teknoprep/racecar-35/hardware/_archive/README.md

# Retired A/B hardware work — not current fabrication deliverables

The active design target is **Rev C**, in `../teensy-integrated-revc/`.

- `teensy-carrier-reva/`: former, unbuilt external-module carrier. Preserved
  unchanged because the C illustration reuses its footprint/3D assets. Its
  Gerbers are NOT the integrated C design. Do not order it as a substitute.
- `teensy-integrated-revb-RETIRED-CONCEPT.tar.gz`: complete snapshot of the former
  B concept (external WiFi antenna, terminals on multiple edges). Superseded.

A/B user-facing Downloads packages were moved into
`/home/chris/Downloads/.retired-racecar-ab/` to prevent accidental ordering.
Nothing here is a Rev C electrical design, circuit approval or fabrication release.
Keep these inputs archival; old scripts may contain historical absolute paths.
