teknoprep/racecar-35/hardware/_archive/teensy-carrier-reva/reports/drill-report.txt

Drill report for racecar-carrier-reva.kicad_pcb
Created on 2026-09-09T08:36:47-0400

Copper Layer Stackup:
    =============================================================
    L1 :  F.Cu                      front
    L2 :  B.Cu                      back

Drill file 'racecar-carrier-reva-PTH.drl' contains
    plated through holes:
    =============================================================
    T1  0.400mm  0.0157"  (11 holes)
    T2  0.800mm  0.0315"  (4 holes)
    T3  0.950mm  0.0374"  (12 holes)
    T4  1.000mm  0.0394"  (78 holes)
    T5  1.300mm  0.0512"  (8 holes)

    Total plated holes count 113

Drill file 'racecar-carrier-reva-NPTH.drl' contains
    unplated through holes:
    =============================================================
    T1  3.200mm  0.1260"  (4 holes)

    Total unplated holes count 4
