teknoprep/racecar-35/crowpanel-arduino/RaceDash_v0139_orig/RaceDash_v0139_orig.ino

// racecar-35 dash — CrowPanel ESP32-S3 7" V3.0
// Built via arduino-cli with esp32:esp32@2.0.14, OPI PSRAM, QIO 4MB.
//
// UART0 (Serial) listens for two line types from the Teensy 4.1, 115200 8N1:
//   GPS,<fix>,<sats>,<lat_deg>,<lon_deg>,<speed_mph>,<heading_deg>,<gps_status>
//   ENG,<rpm>[,<oil_psi_x10>,<coolant_f_x10>]   (3-field form, back-compat to 1)
//
// Two pages, swipeable:
//   PAGE_DASH      — RPM bar + huge speed + L (HDG/LAT/LON) / R (FIX/SATS/GPS)
//   PAGE_SETTINGS  — adjustable thresholds for the RPM bar, alert thresholds,
//                    blink rates and colors. Persisted to NVS via Preferences.
// Swipe right→left enters settings; left→right returns to dash.

#include <Wire.h>
#include <PCA9557.h>
#include <WiFi.h>          // ESP32-S3 built-in WiFi (NTP, OTA HTTPS, future cloud upload)
#include <WiFiClientSecure.h>   // HTTPS to GitHub for manifest + firmware download
#include <HTTPClient.h>         // wraps WiFiClientSecure with a simple GET/POST API
#include <Update.h>             // partition-swap OTA writer
#include <esp_log.h>       // for esp_log_level_set("wifi", ESP_LOG_NONE)
#include <mbedtls/sha256.h>     // OTA artifact integrity check vs manifest sha256

// Compile-time firmware version. Bump via the release process when shipping
// a new build (eventually automated by scripts/release.sh + GitHub Action).
// Settings page displays it; "Check for updates" compares to manifest.json
// from https://raw.githubusercontent.com/teknoprep/racecar-35/main/firmware/.
#define FIRMWARE_VERSION "0.1.39"

#include <Preferences.h>
#include <time.h>
#include <driver/i2c.h>           // I2C_NUM_1 for Touch_GT911 config
#define LGFX_USE_V1
#include <LovyanGFX.hpp>
#include <lgfx/v1/platforms/esp32s3/Panel_RGB.hpp>
#include <lgfx/v1/platforms/esp32s3/Bus_RGB.hpp>

// ---------------------------------------------------------------------------
// Forward type decls — Arduino IDE auto-injects function prototypes at the
// top of the translation unit, so any type used in a function signature must
// be visible BEFORE the first function. Real definitions follow below.
// ---------------------------------------------------------------------------
enum SettingId : uint8_t {
    // Internet block at the very top — picks whether all internet-bound
    // operations route via Teensy/W5500 (Ethernet) or CrowPanel/ESP32-S3 WiFi.
    // SSID/pass/status rows are hidden when Mode=Ethernet.
    ST_INET_MODE = 0,
    ST_WIFI_SSID, ST_WIFI_PASS, ST_WIFI_STATUS,
    ST_RPM_MIN, ST_RPM_MAX, ST_ALERTS,
    ST_A1_RPM, ST_A1_COL, ST_A1_HZ,
    ST_AM_RPM, ST_AM_COL, ST_AM_HZ,
    // Coolant temp warn-color + oil PSI warn-color. Each has a master
    // show toggle, a threshold (°F or PSI), and the warning palette colour.
    ST_SHOW_TEMP, ST_TEMP_WARN_F, ST_TEMP_WARN_COL,
    ST_SHOW_PSI,  ST_PSI_WARN_PSI, ST_PSI_WARN_COL,
    // Sensor data source (Direct / MegaSquirt) + AFR display (MS3 mode only).
    // AFR has both a "too rich" (low) and "too lean" (high) warn threshold;
    // either fires the same colour.
    ST_SENSOR_TYPE,
    ST_SHOW_AFR, ST_AFR_WARN_LO, ST_AFR_WARN_HI, ST_AFR_WARN_COL,
    ST_REC_SD, ST_REC_CLOUD,
    ST_CL_HOST, ST_CL_PORT, ST_CL_PROTO, ST_CL_STREAM,
    ST_CL_AUTH_USER, ST_CL_AUTH_PASS,
    ST_AUTO_TRACK,
    ST_TIMEZONE,    // ENUM: cycle through TIMEZONES[]
    ST_SET_TIME,    // action: open time-set page
    ST_COUNT,
    // Tool-page actions — NOT in the scrollable settings list. They live on
    // PAGE_TOOLS (swipe right from STATUS). Their SettingId values are still
    // useful as keyboard / tap dispatch keys (e.g. ST_OTA_CHECK is what
    // handleSettingsTap looked for; now it's tools/handleToolsTap).
    ST_SD_FORMAT,
    ST_OTA_CHECK,
};
struct NumBounds { uint16_t lo, hi, step; };

// Forward-declared so any auto-prototype generated by the Arduino IDE for
// functions that take a `const TimeZone&` parameter resolves cleanly. The
// full struct definition lives further down with the timezone tables.
struct TimeZone;

// WiFi state machine values (full definition lives next to its tick function
// further down). Forward-declared here because the Arduino IDE / arduino-cli
// auto-injects function prototypes at the top of the TU — anything used in
// a function signature must be visible before the first function.
enum WifiState : uint8_t { WS_OFF = 0, WS_CONNECTING, WS_CONNECTED, WS_FAILED };

// Forward decls for the dash-initiated upload flow. The enum / structs need to
// be visible to the auto-prototype scanner that runs on the first function in
// the TU. wifiConnectedNow() is a helper for ufDoPost so it doesn't have to
// reach into the file-scope `wifi_state` global from above its definition.
enum UploadFlowState : uint8_t {
    UF_IDLE = 0,
    UF_LISTING,         // Q,LIST sent, awaiting Q,FILE / Q,END
    UF_FETCH_HEAD,      // Q,GET sent, awaiting Q,DATA
    UF_STREAMING,       // open TCP socket, writing bytes as Q,L arrives
    UF_STREAM_FINISH,   // EOF sent, draining HTTP response from socket
    UF_DELETING,        // Q,DEL sent, awaiting Q,DEL,OK
    UF_DONE,
};
enum SessionsListState : uint8_t {
    SL_IDLE = 0, SL_LISTING, SL_DELETING,
};
static bool wifiConnectedNow();

// Single key descriptor for both numeric and text keyboards.
struct KbKey {
    int16_t  x, y, w, h;
    const char* label;
    // action: visible char (0..0x7F) is inserted as that char into editBuf.
    // Special codes: 0x01='\b' backspace, 0x02='C' clear, 0x03='D' done,
    //                0x04='X' cancel, 0x05=' ' space.
    char action;
};

#define TFT_BL 2

PCA9557 Out;
Preferences prefs;

// ---------------------------------------------------------------------------
// LovyanGFX driver — V3.0 panel timings + GT911 capacitive touch on I2C 0x14.
// ---------------------------------------------------------------------------
class LGFX : public lgfx::LGFX_Device {
public:
    lgfx::Bus_RGB     _bus_instance;
    lgfx::Panel_RGB   _panel_instance;
    lgfx::Light_PWM   _light_instance;
    lgfx::Touch_GT911 _touch_instance;

    LGFX(void) {
        {
            auto cfg = _panel_instance.config();
            cfg.memory_width  = 800; cfg.memory_height = 480;
            cfg.panel_width   = 800; cfg.panel_height  = 480;
            cfg.offset_x = 0;        cfg.offset_y = 0;
            _panel_instance.config(cfg);
        }
        {
            auto cfg = _bus_instance.config();
            cfg.panel = &_panel_instance;
            cfg.pin_d0  = GPIO_NUM_15; cfg.pin_d1  = GPIO_NUM_7;  cfg.pin_d2  = GPIO_NUM_6;
            cfg.pin_d3  = GPIO_NUM_5;  cfg.pin_d4  = GPIO_NUM_4;
            cfg.pin_d5  = GPIO_NUM_9;  cfg.pin_d6  = GPIO_NUM_46; cfg.pin_d7  = GPIO_NUM_3;
            cfg.pin_d8  = GPIO_NUM_8;  cfg.pin_d9  = GPIO_NUM_16; cfg.pin_d10 = GPIO_NUM_1;
            cfg.pin_d11 = GPIO_NUM_14; cfg.pin_d12 = GPIO_NUM_21; cfg.pin_d13 = GPIO_NUM_47;
            cfg.pin_d14 = GPIO_NUM_48; cfg.pin_d15 = GPIO_NUM_45;
            cfg.pin_henable = GPIO_NUM_41;
            cfg.pin_vsync   = GPIO_NUM_40;
            cfg.pin_hsync   = GPIO_NUM_39;
            cfg.pin_pclk    = GPIO_NUM_0;
            cfg.freq_write  = 15000000;
            cfg.hsync_polarity    = 0;
            cfg.hsync_front_porch = 40;
            cfg.hsync_pulse_width = 48;
            cfg.hsync_back_porch  = 40;
            cfg.vsync_polarity    = 0;
            cfg.vsync_front_porch = 1;
            cfg.vsync_pulse_width = 31;
            cfg.vsync_back_porch  = 13;
            cfg.pclk_active_neg = 1;
            cfg.de_idle_high    = 0;
            cfg.pclk_idle_high  = 0;
            _bus_instance.config(cfg);
            _panel_instance.setBus(&_bus_instance);
        }
        {
            auto cfg = _light_instance.config();
            cfg.pin_bl = GPIO_NUM_2;
            _light_instance.config(cfg);
            _panel_instance.light(&_light_instance);
        }
        {
            auto cfg = _touch_instance.config();
            cfg.x_min      = 0;   cfg.x_max = 799;
            cfg.y_min      = 0;   cfg.y_max = 479;
            cfg.pin_int    = -1;
            cfg.pin_rst    = -1;
            cfg.bus_shared = true;
            cfg.offset_rotation = 0;
            cfg.i2c_port   = I2C_NUM_1;
            cfg.pin_sda    = GPIO_NUM_19;
            cfg.pin_scl    = GPIO_NUM_20;
            cfg.freq       = 400000;
            cfg.i2c_addr   = 0x14;
            _touch_instance.config(cfg);
            _panel_instance.setTouch(&_touch_instance);
        }
        setPanel(&_panel_instance);
    }
};

LGFX tft;

// ---------------------------------------------------------------------------
// Sprite back-buffers for the dynamic dash page regions.
//
// Why: the CrowPanel V3.0 RGB Panel keeps a continuous parallel-RGB scan over
// its framebuffer in PSRAM. When we draw text/shapes directly into that
// framebuffer, the LCD can scan a half-written element and the user sees a
// tear. At 25 Hz telemetry that tear is visible 25 times per second on the
// big-area elements (speed digit, RPM bar, sensor lines).
//
// Fix: render each fast-changing region into its own PSRAM-backed sprite,
// then pushSprite() the whole sprite to the framebuffer in one DMA blit.
// The blit is fast (sub-ms for these sizes on the S3) so the LCD scan rarely
// catches a sprite mid-push, and the user-visible result is a clean atomic
// update of each element. Each sprite is allocated once at boot and reused
// for the life of the process.
//
// Sized generously so even Font7-size-4 "888" (full speed digit) or a long
// "TEMP: 250\xB0F" line fits without clipping.
// ---------------------------------------------------------------------------
namespace {
    LGFX_Sprite spr_rpm_bar(&tft);     // inside the RPM bar border
    LGFX_Sprite spr_rpm_text(&tft);    // RPM number under the bar
    LGFX_Sprite spr_speed(&tft);       // huge centred MPH digits
    LGFX_Sprite spr_temp(&tft);        // "TEMP: ..." line
    LGFX_Sprite spr_psi(&tft);         // "PSI:  ..." line
    LGFX_Sprite spr_afr(&tft);         // "AFR:  ..." line (MS3 mode only)
    LGFX_Sprite spr_rec_badge(&tft);   // REC ● N  /  queue: N  /  REC ? no ack
    LGFX_Sprite spr_fix(&tft);         // FIX value (right column)
    LGFX_Sprite spr_sats(&tft);        // SATS value (right column)
    LGFX_Sprite spr_gps(&tft);         // GPS status value (right column)
    LGFX_Sprite spr_pred(&tft);        // predictive lap time (middle column)
    LGFX_Sprite spr_lap(&tft);         // last lap time (middle column)
    LGFX_Sprite spr_track_name(&tft);  // active track name under TRACK btn
    LGFX_Sprite spr_recbtn(&tft);      // START/STOP button face
    LGFX_Sprite spr_upbtn(&tft);       // manual queue-upload button
}
static bool   dash_sprites_ready = false;

static void setupDashSprites() {
    auto mk = [](LGFX_Sprite& s, int w, int h) -> bool {
        s.setPsram(true);          // request PSRAM backing store
        s.setColorDepth(16);       // match RGB565 panel format
        return s.createSprite(w, h) != nullptr;
    };
    // Inner-of-border for the RPM bar so the static white border outline
    // drawn directly on the framebuffer at pageJustEntered isn't clobbered.
    dash_sprites_ready =
        mk(spr_rpm_bar,    756, 76)  &&
        mk(spr_rpm_text,   110, 26)  &&
        mk(spr_speed,      360, 200) &&    // covers Font7-size-4 (≈192 px tall)
        mk(spr_temp,       240, 38)  &&
        mk(spr_psi,        240, 38)  &&
        mk(spr_afr,        240, 38)  &&
        mk(spr_rec_badge,  220, 22)  &&
        mk(spr_fix,        110, 24)  &&
        mk(spr_sats,        60, 24)  &&
        mk(spr_gps,        110, 24)  &&
        mk(spr_pred,       110, 24)  &&
        mk(spr_lap,        110, 24)  &&
        mk(spr_track_name, 320, 22)  &&
        mk(spr_recbtn,     160, 70)  &&
        mk(spr_upbtn,      180, 70);
    if (dash_sprites_ready) Serial.println("dash sprites: ok");
    else                    Serial.println("WARNING: dash sprite alloc failed \u2014 dash will fall back to direct draw");
}

// ---------------------------------------------------------------------------
// User-pickable color palette for alert colors.
// ---------------------------------------------------------------------------
constexpr int N_PALETTE = 8;
const uint16_t PALETTE[N_PALETTE] = {
    TFT_RED, TFT_ORANGE, TFT_YELLOW, TFT_GREEN,
    TFT_CYAN, TFT_BLUE, TFT_MAGENTA, TFT_WHITE
};
const char* const PALETTE_NAMES[N_PALETTE] = {
    "RED", "ORANGE", "YELLOW", "GREEN",
    "CYAN", "BLUE", "MAGENTA", "WHITE"
};

// ---------------------------------------------------------------------------
// State.
// ---------------------------------------------------------------------------
struct GpsState {
    uint8_t  fix      = 0;
    uint8_t  sats     = 0;
    float    lat_deg  = 0.0f;
    float    lon_deg  = 0.0f;
    float    mph      = 0.0f;
    float    hdg_deg  = 0.0f;
    uint8_t  status   = 0;        // 0=OFF 1=RAW 2=OK 3=STALE
    uint32_t last_ms  = 0;
};
static GpsState g;

struct EngState {
    uint16_t rpm           = 0;
    // x10 fixed-point: 0..30000 PSI*10, -1 on sensor fault. Stored as int16.
    int16_t  oil_psi_x10   = -1;
    int16_t  coolant_f_x10 = -1;
    uint32_t last_ms       = 0;
};
static EngState eng;

// MegaSquirt-via-CAN data, forwarded by the Teensy when the CAN transceiver is
// wired up (planned — see Teensy main.cpp). All fields are x10 fixed-point
// except RPM. -1 indicates "not received" / fault. The dash listens for ECU
// lines only when settings.sensor_type == 1 (MegaSquirt).
struct EcuState {
    uint16_t rpm           = 0;
    int16_t  coolant_f_x10 = -1;
    int16_t  map_x10       = -1;     // manifold absolute pressure, kPa × 10
    int16_t  tps_x10       = -1;     // throttle position, % × 10
    int16_t  afr_x10       = -1;     // air/fuel ratio × 10 (e.g. 145 = 14.5)
    int16_t  iat_f_x10     = -1;     // intake air temp, °F × 10
    int16_t  bat_x10       = -1;     // battery voltage, V × 10
    uint32_t last_ms       = 0;
};
static EcuState ecu;

struct ImuState {
    float    ax = 0, ay = 0, az = 0;   // g  (±2g range)
    float    gx = 0, gy = 0, gz = 0;   // deg/s (±250 range)
    uint32_t last_ms = 0;
};
static ImuState imu;

static char     active_ip[24]    = "NOT CONNECTED";  // updated by ETH, line from Teensy
static uint32_t rec_start_ms     = 0;                // millis() when recording last started

// SD card state — updated from SD,<status>[,<total_mb>[,<free_mb>]] lines.
// 0=NONE  1=NEEDS_FORMAT  2=READY  3=ERROR  4=FORMATTING
static uint8_t  sd_card_status   = 0;
static uint32_t sd_total_mb      = 0;
static uint32_t sd_free_mb       = 0;
static char     sd_err_hex[8]    = "";   // last SdFat err code (hex from SD,NONE,<errcode>)

// Active session state — updated from SD,REC,<0|1>,<file>,<samples> lines.
// The dash uses this to show a REC indicator + a live sample count.
static bool     sd_session_active  = false;
static char     sd_session_file[80] = "";
static uint32_t sd_session_samples = 0;

// ---------------------------------------------------------------------------
// OTA state — driven by tapping "Check for updates" in settings.
// Source of truth lives in firmware/manifest.json on this repo's main branch:
//   https://raw.githubusercontent.com/teknoprep/racecar-35/main/firmware/manifest.json
//
// State machine drives PAGE_OTA modal. otaTick() in loop() advances states
// that perform network work (checking + downloading) without blocking the
// touch handler. Cancel is implemented by setting ota_cancel_requested;
// the tick checks it between chunks and bails.
// ---------------------------------------------------------------------------
enum OtaState : uint8_t {
    OTA_S_IDLE = 0,
    OTA_S_CHECKING,             // GET manifest.json
    OTA_S_UPTODATE,             // version match — nothing to do
    OTA_S_AVAILABLE,            // update found; modal waits for user Confirm/Cancel
    OTA_S_TEENSY_DOWNLOADING,   // download teensy.hex + stream over UART to Teensy
    OTA_S_TEENSY_WAITING,       // hex flushed; wait/poll until Teensy reports target version
    OTA_S_DOWNLOADING,          // streaming CrowPanel firmware bytes into Update.write()
    OTA_S_APPLYING,             // Update.end() in progress (finalising flash partition)
    OTA_S_REBOOT,               // success; about to ESP.restart()
    OTA_S_FAILED,               // any error; modal shows reason + Close
};
static OtaState ota_state              = OTA_S_IDLE;
static char     ota_latest_version[16] = "";
static char     ota_url[200]           = "";
static char     ota_err_msg[80]        = "";
static uint32_t ota_total_bytes        = 0;
static uint32_t ota_done_bytes         = 0;
static char     ota_sha256[80]         = "";   // expected sha256 from manifest (crowpanel)
static char     ota_teensy_sha256[80]  = "";   // expected sha256 from manifest (teensy)
// Teensy OTA uses two visible phases: WiFi download into PSRAM, then
// ACK-paced UART transfer to the Teensy/FlasherX. Keep separate counters so
// the modal doesn't misleadingly show one bar that suddenly slows at 50%.
static uint32_t ota_t_dl_total         = 0;
static uint32_t ota_t_dl_done          = 0;
static uint32_t ota_t_tx_total         = 0;
static uint32_t ota_t_tx_done          = 0;
static uint8_t  ota_return_page        = 0;     // page to restore on Close
static bool     ota_modal_dirty        = false;
static bool     ota_cancel_requested   = false;
// Teensy-side update state (parallel manifest entry)
static char     ota_teensy_version[16] = "";
static char     ota_teensy_url[200]    = "";
static uint32_t ota_teensy_size        = 0;
static bool     ota_need_teensy        = false;
static bool     ota_need_crowpanel     = false;
static bool     ota_teensy_commit_seen = false;   // saw FW,COMMITTING from FlasherX

// Upload modal state — driven by UPLOAD,START/PROG/DONE lines from Teensy.
// While upload_active, the dash forces PAGE_UPLOAD on top of whatever was
// showing, and ignores all input except the CANCEL button. CANCEL latches
// upload_locally_cancelled = true so the dash can show a small reminder that
// uploads are disabled until the system reboots.
static bool     upload_active            = false;
static char     upload_file[64]          = "";
static uint32_t upload_total             = 0;
static uint32_t upload_done              = 0;
static uint8_t  upload_return_page       = 0;        // PAGE_DASH; uint8_t because
                                                     // enum Page isn't visible up here
static bool     upload_locally_cancelled = false;   // cleared only on reboot
static bool     upload_modal_dirty       = false;
static uint32_t upload_last_draw_ms      = 0;
static char     upload_result_msg[180]   = "";       // banner after DONE: status + optional reason

// Cloud state — updated from CLD,<live_ok>,<queue_depth> lines.
static bool     cloud_live_ok      = false;
static uint32_t cloud_queue_depth  = 0;

// Firmware version tracking. Dash version is compile-time (FIRMWARE_VERSION).
// Teensy version arrives via VER,teensy,<ver> on Teensy boot, and on demand
// when the dash sends "VER?\n" (dash boot + status page entry).
static char     teensy_fw_version[16] = "?";

// Two-tap arming for the SD format action in settings.
static bool     sd_format_armed  = false;
static uint32_t sd_format_arm_ms = 0;

// Settings page dirty flag — declared here (before the UART parsers) so
// parseSdLine() can set it on status change. The settings page checks it
// each draw cycle to decide whether to repaint.
static bool settingsDirty = true;

// RTC epoch received from the Teensy's TIME, line (0 = not yet received).
static uint32_t rtc_epoch = 0;

// Time-set page editing state — populated from rtc_epoch on entry.
static int  ts_year  = 2025, ts_month = 1, ts_day  = 1;
static int  ts_hour  = 0,    ts_min   = 0, ts_sec  = 0;
static bool ts_dirty = false;   // set by +/- taps; triggers value redraw

// ---------------------------------------------------------------------------
// Lap timer — GPS-proximity start/finish detection + distance integration.
// ---------------------------------------------------------------------------
struct LapTimer {
    bool     active          = false;
    int      track_idx       = -1;    // which TRACKS[] entry we're timing at
    uint32_t lap_start_ms    = 0;
    float    dist_miles      = 0.0f;  // odometer this lap (mph * dt)
    uint32_t prev_gps_ms     = 0;
    bool     left_start      = false; // true once car has moved away from S/F line
    bool     timing_started  = false; // true after first clean S/F crossing (guards partial first lap)

    uint32_t last_lap_ms     = 0;     // most recent completed lap time (0 = none)
    float    last_lap_dist   = 0.0f;  // distance of last completed lap (miles)
};
static LapTimer lapTimer;

constexpr float    LAP_RADIUS_KM = 0.075f;   // 75 m start/finish detection radius
constexpr uint32_t MIN_LAP_MS    = 15000;    // minimum lap time before a crossing counts

// Recording state — toggled by the START/STOP button on the dash. Sent to
// the Teensy as `REC,<0|1>\n` on UART0 TX. The Teensy doesn't read this
// yet (one-way bytes harmlessly accumulate in its Serial3 RX buffer);
// when the SD-card / cloud-streaming feature is implemented Teensy-side
// it just starts consuming the line.
static bool recording         = false;
static int  last_track_idx    = -1;        // TRACKS[] index of the last confirmed track (-1 = none saved)
static char active_track_name[52] = "";    // full display name (may include config, e.g. "Mid-Ohio Full Course")

// Button geometry on the dash page — both buttons sit left of the speed.
// START/STOP is smaller and higher than before; TRACK button lives below it.
namespace {
  constexpr int RECBTN_X = 30;
  constexpr int RECBTN_Y = 155;
  constexpr int RECBTN_W = 160;
  constexpr int RECBTN_H = 70;
  constexpr int TRKBTN_X = 30;    // always-visible shortcut to the track picker
  constexpr int TRKBTN_Y = 235;   // RECBTN_Y + RECBTN_H + 10
  constexpr int TRKBTN_W = 160;
  constexpr int TRKBTN_H = 60;
  // Manual queue-upload button. Shows only when there is a backlog of
  // sessions waiting in /queue/ AND we aren't currently recording. Sits in
  // the empty band between the START button and the big speed digit.
  constexpr int UPBTN_X = 210;
  constexpr int UPBTN_Y = 155;
  constexpr int UPBTN_W = 180;
  constexpr int UPBTN_H = 70;
  // Speed sits on the right side of the screen (out of the way of the
  // START/STOP button on the left). Drop the decimal at >=100 mph so a
  // 3-digit number stays narrow enough to fit the 400-px bg pad cleanly
  // without clipping at the right edge.
  // Speed is integer MPH only (no decimal), so the layout never has to budget
  // for a decimal point that vanishes at >= 100 mph. With 3 digits max we can
  // pull the centre slightly inward from the right panel edge for breathing
  // room around the largest values.
  constexpr int SPEED_CX    = 580;       // speed text middle-centre x
  constexpr int SPEED_PAD_W = 360;       // bg-fill pad width (spans 400..760)
}

struct Settings {
    // RPM bar + alert flash (existing)
    uint16_t rpm_min          = 1000;
    uint16_t rpm_max          = 8000;
    bool     alerts_enabled   = true;
    uint16_t alert1_rpm       = 6000;
    uint8_t  alert1_color_idx = 2;     // YELLOW
    uint8_t  alert1_hz        = 2;
    uint16_t alertmax_rpm     = 7500;
    uint8_t  alertmax_color_idx = 0;   // RED
    uint8_t  alertmax_hz      = 8;

    // Recording / streaming
    bool     record_sd        = false;
    bool     record_cloud     = false;
    char     cloud_host[64]   = "racecar.api.blueuc.com";  // default endpoint
    uint16_t cloud_port       = 80;
    uint8_t  cloud_protocol   = 1;     // 0=HTTP, 1=HTTPS, 2=FTP (default HTTPS; FTP NYI)
    uint8_t  cloud_stream     = 1;     // 0=Live, 1=AfterRace (default AfterRace; WiFi forces AfterRace anyway)
    // cloud_user repurposed as a free-text USER EMAIL tag for data ownership.
    // Not an auth credential — the Teensy forwards it as X-User-Email header.
    // Real auth (Google OAuth) lives in the cloud-side Docker image.
    char     cloud_auth_user[64] = "";   // user email (X-User-Email)
    char     cloud_auth_pass[96] = "";   // API key (X-API-Key); masked on display

    // Internet routing. 0=Ethernet (Teensy/W5500), 1=WiFi (CrowPanel ESP32-S3).
    // Phase 1: controls NTP path + (future) firmware update path. Cloud upload
    // routing still flows through Teensy/Ethernet regardless until Phase 3.
    uint8_t  internet_mode    = 0;       // default Ethernet
    char     wifi_ssid[33]    = "";      // 802.11 max 32 + NUL
    char     wifi_pass[64]    = "";      // WPA2 PSK max 63 + NUL

    // Engine sensor display + warn thresholds (drawn bottom-left on the dash).
    // show_*  : false hides that line entirely from the dash.
    // *_warn  : threshold past which the value flips to the warn colour.
    //           Coolant warns ABOVE the threshold (overheat), oil warns BELOW
    //           it (low pressure — engine-killing if you don't see it).
    bool     show_coolant       = true;
    uint16_t coolant_warn_f     = 220;     // °F — typical 220°F overheat threshold
    uint8_t  coolant_warn_col   = 0;       // RED
    bool     show_oil_psi       = true;
    uint16_t oil_warn_psi       = 20;      // PSI — typical 20 PSI low-oil floor
    uint8_t  oil_warn_col       = 0;       // RED

    // Sensor data source. Selects which UART line type the dash trusts for
    // engine telemetry that exists in both pipelines (coolant temp today; RPM
    // and others as MS3 CAN comes online):
    //   0 = Direct     — Teensy ADCs on A2/A3 (the wiring we built in §5b/5c)
    //   1 = MegaSquirt — MS3 CAN broadcast, forwarded by Teensy as ECU,...
    // Oil PSI stays direct regardless (MS3 typically doesn't have an oil
    // pressure input wired). AFR is only available in MegaSquirt mode.
    uint8_t  sensor_type        = 0;       // default Direct

    // AFR (Air/Fuel Ratio) — only meaningful in MegaSquirt sensor mode.
    // Two-sided warn band: too rich (< afr_warn_lo) and too lean (> afr_warn_hi)
    // both flip the value to the warn colour. Values are AFR × 10 (so 145 = 14.5).
    bool     show_afr           = true;
    uint16_t afr_warn_lo_x10    = 115;     // 11.5 AFR — below this is dangerously rich
    uint16_t afr_warn_hi_x10    = 160;     // 16.0 AFR — above this is dangerously lean
    uint8_t  afr_warn_col       = 0;       // RED

    // Track selection
    bool     auto_select_track = true; // when on, skip picker if a clear closest match exists

    // Time zone — index into TIMEZONES[] (defined below). Display only;
    // the Teensy's RTC + the wire-format TIME line are always UTC.
    uint8_t  timezone_idx     = 0;     // default UTC
};
static Settings s;

// Names for ENUM-style settings (cycle-on-tap).
const char* const PROTOCOL_NAMES[] = { "HTTP", "HTTPS", "FTP" };
constexpr int N_PROTOCOL = 3;
const char* const STREAM_NAMES[]   = { "Live Stream", "After Race" };
constexpr int N_STREAM   = 2;
const char* const SENSOR_TYPE_NAMES[] = { "Direct", "MegaSquirt" };
constexpr int N_SENSOR_TYPE = 2;
const char* const INET_MODE_NAMES[]   = { "Ethernet", "WiFi" };
constexpr int N_INET_MODE   = 2;

// ---------------------------------------------------------------------------
// Time zones with DST rules.
//
// The Teensy emits UTC always (TIME,<unix_epoch>). All DST/offset math is
// done here in the dash for display purposes. We send TZ,<id> to the Teensy
// at boot and on change so the trunk-side has the info available for future
// SD-filename / cloud-metadata use, but the Teensy doesn't currently apply
// the offset itself.
//
// DST rule fields:
//   stdOffsetHr   standard-time offset from UTC in hours (-5 = EST, +0 = GMT)
//   observesDst   true if DST applies (false for AZ, HI, UTC, etc.)
//   dstStart{Month,Week,Dow,Hour}   "Nth weekday of month, at HH local std time"
//   dstEnd{Month,Week,Dow,Hour}     same shape; week 1-4 = nth, 5 = last
// ---------------------------------------------------------------------------
struct TimeZone {
    const char* id;            // short id sent to Teensy ("UTC", "ET", "PT", ...)
    const char* name;          // long name shown in the settings ENUM cycle
    const char* abbrevStd;     // abbreviation when in standard time ("EST")
    const char* abbrevDst;     // abbreviation when in DST ("EDT"); == abbrevStd if no DST
    int8_t      stdOffsetHr;
    bool        observesDst;
    uint8_t     dstStartMonth;  // 1-12
    uint8_t     dstStartWeek;   // 1-4 (nth) or 5 (last)
    uint8_t     dstStartDow;    // 0=Sun .. 6=Sat
    uint8_t     dstStartHour;   // local std hour at which DST begins
    uint8_t     dstEndMonth;
    uint8_t     dstEndWeek;
    uint8_t     dstEndDow;
    uint8_t     dstEndHour;
};

// Common US zones + a few internationals. Add more by extending this array.
// US DST: 2nd Sunday of March → 1st Sunday of November (since 2007).
// EU DST: last Sunday of March → last Sunday of October.
static const TimeZone TIMEZONES[] = {
    // id      name                  std    dst    off  dst   sM sW sD sH eM eW eD eH
    { "UTC",   "UTC",                "UTC", "UTC",  0,  false, 0, 0, 0, 0, 0, 0, 0, 0 },
    { "ET",    "Eastern (US)",       "EST", "EDT", -5, true,   3, 2, 0, 2, 11, 1, 0, 2 },
    { "CT",    "Central (US)",       "CST", "CDT", -6, true,   3, 2, 0, 2, 11, 1, 0, 2 },
    { "MT",    "Mountain (US)",      "MST", "MDT", -7, true,   3, 2, 0, 2, 11, 1, 0, 2 },
    { "MT-AZ", "Arizona (no DST)",   "MST", "MST", -7, false,  0, 0, 0, 0, 0, 0, 0, 0 },
    { "PT",    "Pacific (US)",       "PST", "PDT", -8, true,   3, 2, 0, 2, 11, 1, 0, 2 },
    { "AKT",   "Alaska",             "AKST","AKDT",-9, true,   3, 2, 0, 2, 11, 1, 0, 2 },
    { "HT",    "Hawaii (no DST)",    "HST", "HST",-10, false,  0, 0, 0, 0, 0, 0, 0, 0 },
    { "GMT",   "UK (London)",        "GMT", "BST",  0, true,   3, 5, 0, 1, 10, 5, 0, 1 },
    { "CET",   "Europe (Paris)",     "CET", "CEST", 1, true,   3, 5, 0, 2, 10, 5, 0, 2 },
};
constexpr int N_TIMEZONES = sizeof(TIMEZONES) / sizeof(TIMEZONES[0]);

// Days in month (Gregorian). Leap years = divisible by 4 except centuries
// not divisible by 400.
static int daysInMonth(int y, int m) {
    static const int dom[] = {0,31,28,31,30,31,30,31,31,30,31,30,31};
    const bool leap = (y % 4 == 0 && y % 100 != 0) || (y % 400 == 0);
    return (m == 2 && leap) ? 29 : dom[m];
}

// Day-of-week for a Gregorian date. Zeller's congruence, normalised to
// 0=Sunday, 1=Monday ... 6=Saturday.
static int dayOfWeek(int y, int m, int d) {
    if (m < 3) { y--; m += 12; }
    const int K = y % 100;
    const int J = y / 100;
    const int h = (d + (13 * (m + 1)) / 5 + K + K / 4 + J / 4 + 5 * J) % 7;
    // Zeller h: 0=Sat, 1=Sun, 2=Mon, ..., 6=Fri → shift to 0=Sun
    return (h + 6) % 7;
}

// Day-of-month for the Nth occurrence of a given weekday in a given month.
// nth: 1..4 = literal, 5 = "last".
static int nthWeekdayOfMonth(int year, int month, int targetDow, int nth) {
    const int firstDow         = dayOfWeek(year, month, 1);
    const int firstOccurrence  = ((targetDow - firstDow + 7) % 7) + 1;
    if (nth >= 5) {
        // Last occurrence: walk forward by 7 until next would overshoot the month.
        const int dim = daysInMonth(year, month);
        int d = firstOccurrence;
        while (d + 7 <= dim) d += 7;
        return d;
    }
    return firstOccurrence + 7 * (nth - 1);
}

// Is DST currently in effect for the given UTC epoch under the given zone?
// We compare against local *standard* time so the rule's "2 AM local" maps
// cleanly to a single instant per year (we don't try to resolve the
// 2:00–3:00 AM "spring-forward" gap or 1:00–2:00 AM "fall-back" overlap;
// those edge cases are sub-second and not worth the complexity here).
static bool isDstActive(time_t utc, const TimeZone& tz) {
    if (!tz.observesDst) return false;

    const time_t   localStd = utc + (time_t)tz.stdOffsetHr * 3600;
    struct tm*     tmv = gmtime(&localStd);
    const int year  = tmv->tm_year + 1900;
    const int month = tmv->tm_mon + 1;
    const int day   = tmv->tm_mday;
    const int hour  = tmv->tm_hour;

    const int dstStartDay = nthWeekdayOfMonth(year, tz.dstStartMonth, tz.dstStartDow, tz.dstStartWeek);
    const int dstEndDay   = nthWeekdayOfMonth(year, tz.dstEndMonth,   tz.dstEndDow,   tz.dstEndWeek);

    // Outside the months containing the transitions: easy.
    if (month > tz.dstStartMonth && month < tz.dstEndMonth) return true;
    if (month < tz.dstStartMonth || month > tz.dstEndMonth) return false;

    // Same month as start (or end): compare day, then hour.
    if (month == tz.dstStartMonth) {
        if (day != dstStartDay) return day > dstStartDay;
        return hour >= tz.dstStartHour;
    }
    // month == dstEndMonth
    if (day != dstEndDay) return day < dstEndDay;
    return hour < tz.dstEndHour;
}

// UTC offset in seconds (negative for west of UTC), accounting for DST.
static int32_t tzOffsetSeconds(time_t utc, const TimeZone& tz) {
    int32_t off = (int32_t)tz.stdOffsetHr * 3600;
    if (isDstActive(utc, tz)) off += 3600;
    return off;
}

// UTC → local epoch (seconds). Result can be passed to gmtime() to format.
static time_t utcToLocal(time_t utc, const TimeZone& tz) {
    return utc + tzOffsetSeconds(utc, tz);
}

// Local → UTC. Used when the user hand-enters a time via the time-set page.
// Computes the offset by approximating DST status from a near-UTC estimate;
// only ambiguous within the spring/fall transition hour, which we accept.
static time_t localToUtc(time_t local, const TimeZone& tz) {
    int32_t off = (int32_t)tz.stdOffsetHr * 3600;
    const time_t utcApprox = local - off;
    if (isDstActive(utcApprox, tz)) off += 3600;
    return local - off;
}

// Returns the abbreviation appropriate for the given UTC moment ("EST"/"EDT").
static const char* tzAbbrevFor(time_t utc, const TimeZone& tz) {
    return isDstActive(utc, tz) ? tz.abbrevDst : tz.abbrevStd;
}

// Build a UTC unix epoch from broken-down UTC fields. (Used by time-set SAVE.)
static uint32_t makeEpochUtc(int y, int mo, int d, int h, int mi, int s) {
    static const int dom[] = {0,31,28,31,30,31,30,31,31,30,31,30,31};
    uint32_t days = 0;
    for (int yr = 1970; yr < y; yr++) {
        days += 365 + (((yr % 4 == 0 && yr % 100 != 0) || yr % 400 == 0) ? 1 : 0);
    }
    for (int m = 1; m < mo; m++) {
        days += dom[m];
        if (m == 2 && ((y % 4 == 0 && y % 100 != 0) || y % 400 == 0)) days++;
    }
    days += d - 1;
    return (uint32_t)days * 86400UL + (uint32_t)h * 3600UL + (uint32_t)mi * 60UL + (uint32_t)s;
}

// ---------------------------------------------------------------------------
// Track database — pre-seeded list of common US road-course tracks. Stored
// alphabetically (the picker re-orders on the fly when GPS is available).
// Add tracks by extending this array OR (TODO) editing via the settings page.
// ---------------------------------------------------------------------------
struct TrackConfig { const char* name; };

struct TrackInfo {
    const char* name;
    float       lat;                    // track centre (used for "are you at this track?")
    float       lon;
    float       radius_km;
    float       sf_lat;                 // start/finish line (used for lap detection)
    float       sf_lon;                 // NOTE: all S/F coords are approximate — verify on-site
    const TrackConfig* configs;         // nullptr = single layout, no config sub-picker
    uint8_t            n_configs;       // 0 = single layout
};
// Config arrays — tracks with multiple layouts that share the same S/F line.
// Layouts with genuinely different S/F locations get separate TRACKS[] entries.
static const TrackConfig MID_OHIO_CFGS[] = { {"Full + Chicane"}, {"Full Course"}, {"Short Course"} };
static const TrackConfig SONOMA_CFGS[]   = { {"Full Course"}, {"Short Course"} };
static const TrackConfig WGL_CFGS[]      = { {"Grand Prix"}, {"Short Course"} };
static const TrackConfig VIR_CFGS[]      = { {"Full Course"}, {"Grand Course"}, {"North Course"} };

static const TrackInfo TRACKS[] = {
    // name                     centre lat/lon           radius  S/F lat/lon               configs       n
    { "Barber",        33.5328f,  -86.6181f, 2.5f,  33.5327f,  -86.6155f, nullptr,         0 },
    { "CMP Full",      34.4884f,  -80.5941f, 2.0f,  34.4870f,  -80.5955f, nullptr,         0 },
    { "CMP East",      34.4870f,  -80.5880f, 1.2f,  34.4840f,  -80.5880f, nullptr,         0 },
    { "CMP West",      34.4884f,  -80.6000f, 1.0f,  34.4900f,  -80.6000f, nullptr,         0 },
    { "COTA",          30.1328f,  -97.6411f, 3.0f,  30.1341f,  -97.6413f, nullptr,         0 },
    { "Daytona",       29.1853f,  -81.0697f, 3.0f,  29.1868f,  -81.0700f, nullptr,         0 },
    { "Laguna Seca",   36.5847f, -121.7494f, 2.5f,  36.5843f, -121.7530f, nullptr,         0 },
    { "Lime Rock",     41.9263f,  -73.3856f, 2.0f,  41.9271f,  -73.3821f, nullptr,         0 },
    { "Mid-Ohio",      40.6889f,  -82.6356f, 2.5f,  40.6895f,  -82.6375f, MID_OHIO_CFGS,   3 },
    { "Nelson Ledges", 41.3892f,  -81.0852f, 1.5f,  41.3899f,  -81.0858f, nullptr,         0 },
    { "NHMS",          43.3628f,  -71.4630f, 2.0f,  43.3600f,  -71.4640f, nullptr,         0 },
    { "NJMP Thunderbolt", 39.4053f, -75.0789f, 2.0f, 39.4079f, -75.0793f, nullptr,         0 },
    { "NJMP Lightning",   39.3998f, -75.0735f, 1.5f, 39.4008f, -75.0728f, nullptr,         0 },
    { "Pocono",        41.0561f,  -75.5128f, 3.5f,  41.0550f,  -75.5115f, nullptr,         0 },
    { "Road America",  43.7986f,  -87.9956f, 3.0f,  43.7963f,  -87.9944f, nullptr,         0 },
    { "Road Atlanta",  34.1469f,  -83.8189f, 2.5f,  34.1518f,  -83.8197f, nullptr,         0 },
    { "Sebring",       27.4570f,  -81.3568f, 3.5f,  27.4502f,  -81.3537f, nullptr,         0 },
    { "Sonoma",        38.1614f, -122.4544f, 2.5f,  38.1615f, -122.4547f, SONOMA_CFGS,     2 },
    { "Summit Pt",           39.2415f, -77.9779f, 1.5f, 39.2415f, -77.9779f, nullptr,      0 },
    { "Summit Pt Jefferson", 39.2370f, -77.9700f, 1.2f, 39.2370f, -77.9700f, nullptr,      0 },
    { "Summit Pt Shenandoah",39.2450f, -77.9650f, 1.5f, 39.2450f, -77.9650f, nullptr,      0 },
    { "VIR",           36.5611f,  -79.2103f, 2.5f,  36.5689f,  -79.2067f, VIR_CFGS,        3 },
    { "VIR South",     36.5620f,  -79.2100f, 1.2f,  36.5620f,  -79.2100f, nullptr,         0 },
    { "VIR Patriot",   36.5660f,  -79.2120f, 1.0f,  36.5660f,  -79.2120f, nullptr,         0 },
    { "Watkins Glen",  42.3417f,  -76.9272f, 2.5f,  42.3369f,  -76.9272f, WGL_CFGS,        2 },
};
constexpr int N_TRACKS = sizeof(TRACKS) / sizeof(TRACKS[0]);

// Great-circle distance, kilometres. Standard haversine.
static float trackDistanceKm(float lat1, float lon1, float lat2, float lon2) {
    const float DEG2RAD = (float)M_PI / 180.0f;
    const float dLat = (lat2 - lat1) * DEG2RAD;
    const float dLon = (lon2 - lon1) * DEG2RAD;
    const float a = sinf(dLat * 0.5f) * sinf(dLat * 0.5f)
                  + cosf(lat1 * DEG2RAD) * cosf(lat2 * DEG2RAD)
                  * sinf(dLon * 0.5f) * sinf(dLon * 0.5f);
    return 6371.0f * 2.0f * atan2f(sqrtf(a), sqrtf(1.0f - a));
}

// Returns index of closest track within its radius, OR -1 if no GPS / no
// track in range. Used both for "auto select" and to highlight in the picker.
static int closestTrackIdx() {
    if (g.fix < 2) return -1;            // no usable fix
    int   best   = -1;
    float bestKm = 1e9f;
    for (int i = 0; i < N_TRACKS; ++i) {
        const float km = trackDistanceKm(g.lat_deg, g.lon_deg,
                                         TRACKS[i].lat, TRACKS[i].lon);
        if (km <= TRACKS[i].radius_km && km < bestKm) {
            bestKm = km; best = i;
        }
    }
    return best;
}

// ---------------------------------------------------------------------------
// Track picker state. Defined here (not next to its drawing code) so
// handleTouch() can read tp.scrollY / tp.dirty for drag-scroll without
// type-ordering dance.
// ---------------------------------------------------------------------------
struct TrackPickerState {
    uint8_t order[N_TRACKS + 1];   // indices into TRACKS[], +1 for the synthetic UNKNOWN slot
    uint8_t count;                 // total entries displayed
    int8_t  selected;              // index within `order`, -1 = nothing selected
    int     scrollY;
    bool    dirty;
    bool    for_recording = false; // true = confirm starts REC,1; false = track-select only
};
static TrackPickerState tp;

// Config picker — shown after track selection when the track has multiple
// layouts sharing the same S/F line. Tap-only (no scroll; max 3 configs).
struct ConfigPickerState {
    int   track_idx    = -1;
    int8_t selected    =  0;
    bool   dirty       = true;
    bool   from_auto   = false;  // true = opened via GPS auto-select on START; CANCEL → dash
    bool   for_recording = false; // true = confirm starts REC,1; false = track-select only
};
static ConfigPickerState cp;

constexpr uint8_t TP_UNKNOWN_IDX = 0xFE;   // sentinel meaning "synthetic UNKNOWN entry"
constexpr int TP_HDR_H        = 60;
constexpr int TP_FTR_H        = 70;
constexpr int TP_BODY_TOP     = TP_HDR_H;
constexpr int TP_BODY_BOTTOM  = 480 - TP_FTR_H;
constexpr int TP_BODY_HEIGHT  = TP_BODY_BOTTOM - TP_BODY_TOP;
constexpr int TP_ROW_DY       = 40;
constexpr int TP_ROW_HEIGHT   = 36;

static void clampPickerScroll();              // forward — body lives further down

static void loadSettings() {
    prefs.begin("dash", true);
    s.rpm_min            = prefs.getUShort("rpm_min",  s.rpm_min);
    s.rpm_max            = prefs.getUShort("rpm_max",  s.rpm_max);
    s.alerts_enabled     = prefs.getBool  ("alerts",   s.alerts_enabled);
    s.alert1_rpm         = prefs.getUShort("a1_rpm",   s.alert1_rpm);
    s.alert1_color_idx   = prefs.getUChar ("a1_col",   s.alert1_color_idx);
    s.alert1_hz          = prefs.getUChar ("a1_hz",    s.alert1_hz);
    s.alertmax_rpm       = prefs.getUShort("am_rpm",   s.alertmax_rpm);
    s.alertmax_color_idx = prefs.getUChar ("am_col",   s.alertmax_color_idx);
    s.alertmax_hz        = prefs.getUChar ("am_hz",    s.alertmax_hz);
    s.record_sd          = prefs.getBool  ("rec_sd",   s.record_sd);
    s.record_cloud       = prefs.getBool  ("rec_cl",   s.record_cloud);
    prefs.getString      ("cl_host",  s.cloud_host, sizeof(s.cloud_host));
    s.cloud_port         = prefs.getUShort("cl_port",  s.cloud_port);
    s.cloud_protocol     = prefs.getUChar ("cl_proto", s.cloud_protocol);
    s.cloud_stream       = prefs.getUChar ("cl_strm",  s.cloud_stream);
    // Renamed in NVS: cl_user -> cl_email, cl_pass -> cl_key. Old key reads
    // are kept as fallback for one release so existing dashes don't lose
    // their settings on upgrade. Drop after a deploy or two.
    if (prefs.isKey("cl_email")) prefs.getString("cl_email", s.cloud_auth_user, sizeof(s.cloud_auth_user));
    else                          prefs.getString("cl_user",  s.cloud_auth_user, sizeof(s.cloud_auth_user));
    if (prefs.isKey("cl_key"))    prefs.getString("cl_key",   s.cloud_auth_pass, sizeof(s.cloud_auth_pass));
    else                          prefs.getString("cl_pass",  s.cloud_auth_pass, sizeof(s.cloud_auth_pass));
    // Long API keys (>47 chars) saved under the old smaller buffer would be
    // truncated. NVS only stores what was put, so if the value present is
    // shorter than the new buffer that's fine; nothing extra to do.
    s.auto_select_track  = prefs.getBool  ("auto_trk", s.auto_select_track);
    s.timezone_idx       = prefs.getUChar ("tz",       s.timezone_idx);
    s.internet_mode      = prefs.getUChar ("inet",     s.internet_mode);
    prefs.getString      ("wssid",    s.wifi_ssid, sizeof(s.wifi_ssid));
    prefs.getString      ("wpass",    s.wifi_pass, sizeof(s.wifi_pass));
    s.show_coolant       = prefs.getBool  ("s_temp",   s.show_coolant);
    s.coolant_warn_f     = prefs.getUShort("t_warn",   s.coolant_warn_f);
    s.coolant_warn_col   = prefs.getUChar ("t_col",    s.coolant_warn_col);
    s.show_oil_psi       = prefs.getBool  ("s_psi",    s.show_oil_psi);
    s.oil_warn_psi       = prefs.getUShort("p_warn",   s.oil_warn_psi);
    s.oil_warn_col       = prefs.getUChar ("p_col",    s.oil_warn_col);
    s.sensor_type        = prefs.getUChar ("srctyp",   s.sensor_type);
    s.show_afr           = prefs.getBool  ("s_afr",    s.show_afr);
    s.afr_warn_lo_x10    = prefs.getUShort("afr_lo",   s.afr_warn_lo_x10);
    s.afr_warn_hi_x10    = prefs.getUShort("afr_hi",   s.afr_warn_hi_x10);
    s.afr_warn_col       = prefs.getUChar ("afr_col",  s.afr_warn_col);
    if (s.timezone_idx >= N_TIMEZONES) s.timezone_idx = 0;   // sanitise stale NVS
    {
        char ltrk[64] = "";
        prefs.getString("last_trk",   ltrk,               sizeof(ltrk));
        prefs.getString("last_trk_d", active_track_name,  sizeof(active_track_name));
        last_track_idx = -1;
        for (int i = 0; i < N_TRACKS; ++i) {
            if (strcmp(TRACKS[i].name, ltrk) == 0) { last_track_idx = i; break; }
        }
        // If no display name was saved yet, fall back to the base track name.
        if (active_track_name[0] == '\0' && last_track_idx >= 0)
            strncpy(active_track_name, TRACKS[last_track_idx].name, sizeof(active_track_name) - 1);
    }
    prefs.end();
}

static void saveSettings() {
    prefs.begin("dash", false);
    prefs.putUShort("rpm_min",  s.rpm_min);
    prefs.putUShort("rpm_max",  s.rpm_max);
    prefs.putBool  ("alerts",   s.alerts_enabled);
    prefs.putUShort("a1_rpm",   s.alert1_rpm);
    prefs.putUChar ("a1_col",   s.alert1_color_idx);
    prefs.putUChar ("a1_hz",    s.alert1_hz);
    prefs.putUShort("am_rpm",   s.alertmax_rpm);
    prefs.putUChar ("am_col",   s.alertmax_color_idx);
    prefs.putUChar ("am_hz",    s.alertmax_hz);
    prefs.putBool  ("rec_sd",   s.record_sd);
    prefs.putBool  ("rec_cl",   s.record_cloud);
    prefs.putString("cl_host",  s.cloud_host);
    prefs.putUShort("cl_port",  s.cloud_port);
    prefs.putUChar ("cl_proto", s.cloud_protocol);
    prefs.putUChar ("cl_strm",  s.cloud_stream);
    prefs.putString("cl_email", s.cloud_auth_user);   // user email
    prefs.putString("cl_key",   s.cloud_auth_pass);   // API key
    // Clean up the renamed legacy keys so they don't shadow the new ones on
    // next boot's loadSettings() (the load path prefers cl_email/cl_key if
    // present, but stale cl_user/cl_pass values are confusing in debug dumps).
    if (prefs.isKey("cl_user")) prefs.remove("cl_user");
    if (prefs.isKey("cl_pass")) prefs.remove("cl_pass");
    prefs.putBool  ("auto_trk", s.auto_select_track);
    // (sendCfgToTeensy() is called at end of this function so any save also
    // re-syncs the cloud config to the Teensy.)
    prefs.putUChar ("tz",       s.timezone_idx);
    prefs.putUChar ("inet",     s.internet_mode);
    prefs.putString("wssid",    s.wifi_ssid);
    prefs.putString("wpass",    s.wifi_pass);
    prefs.putBool  ("s_temp",   s.show_coolant);
    prefs.putUShort("t_warn",   s.coolant_warn_f);
    prefs.putUChar ("t_col",    s.coolant_warn_col);
    prefs.putBool  ("s_psi",    s.show_oil_psi);
    prefs.putUShort("p_warn",   s.oil_warn_psi);
    prefs.putUChar ("p_col",    s.oil_warn_col);
    prefs.putUChar ("srctyp",   s.sensor_type);
    prefs.putBool  ("s_afr",    s.show_afr);
    prefs.putUShort("afr_lo",   s.afr_warn_lo_x10);
    prefs.putUShort("afr_hi",   s.afr_warn_hi_x10);
    prefs.putUChar ("afr_col",  s.afr_warn_col);
    prefs.end();
    sendCfgToTeensy();   // keep Teensy in sync after every settings save
}

// Push the runtime config the Teensy needs to do cloud uploads. Format:
//   CFG,<key>,<value>\n   (one line per setting; Teensy stores in g_cfg)
// Call after loadSettings() at boot and at the end of saveSettings(). The
// Teensy parser tolerates unknown keys, so we can grow this list freely.
static void sendCfgToTeensy() {
    Serial.printf("CFG,cl_host,%s\n",   s.cloud_host);
    Serial.printf("CFG,cl_port,%u\n",   (unsigned)s.cloud_port);
    Serial.printf("CFG,cl_proto,%u\n",  (unsigned)s.cloud_protocol);
    Serial.printf("CFG,cl_strm,%u\n",   (unsigned)s.cloud_stream);
    Serial.printf("CFG,cl_email,%s\n",  s.cloud_auth_user);
    Serial.printf("CFG,cl_key,%s\n",    s.cloud_auth_pass);
    Serial.printf("CFG,rec_sd,%d\n",    (int)s.record_sd);
    Serial.printf("CFG,rec_cl,%d\n",    (int)s.record_cloud);
    Serial.printf("CFG,inet,%u\n",      (unsigned)s.internet_mode);
}

static void saveLastTrack(int idx, const char* display_name = nullptr) {
    if (idx < 0 || idx >= N_TRACKS) return;
    last_track_idx = idx;
    const char* dn = display_name ? display_name : TRACKS[idx].name;
    strncpy(active_track_name, dn, sizeof(active_track_name) - 1);
    active_track_name[sizeof(active_track_name) - 1] = '\0';
    prefs.begin("dash", false);
    prefs.putString("last_trk",   TRACKS[idx].name);
    prefs.putString("last_trk_d", active_track_name);
    prefs.end();
}

// ---------------------------------------------------------------------------
// Page state machine.
// ---------------------------------------------------------------------------
enum Page : uint8_t {
    PAGE_DASH          = 0,
    PAGE_SETTINGS      = 1,
    PAGE_NUM_KB        = 2,
    PAGE_TEXT_KB       = 3,
    PAGE_TRACK_PICKER  = 4,
    PAGE_CONFIG_PICKER = 5,
    PAGE_STATUS        = 6,
    PAGE_TIME_SET      = 7,
    PAGE_WIFI_SCAN     = 8,
    PAGE_UPLOAD        = 9,   // full-screen modal during file upload; blocks all other input
    PAGE_OTA           = 10,  // full-screen modal during firmware update check / install
    PAGE_TOOLS         = 11,  // maintenance actions: Check for updates, Format SD
    PAGE_SESSIONS      = 12,  // queued NDJSON sessions: select + delete + delete all
};
static Page    currentPage     = PAGE_DASH;
static bool    pageJustEntered = true;

// Keyboard popup state — shared between the numeric (port) and text (host)
// keyboards. editBuf is mutated by tap handlers; on DONE we copy it back to
// the target setting.
struct KeyboardState {
    SettingId target = ST_RPM_MIN;       // which setting we're editing
    char      editBuf[96] = "";          // 95 char value max (fits SHA-256 hex + b64 etc.)
    uint8_t   editLen     = 0;
    bool      shift       = false;       // SHIFT (caps-lock) state for text keyboard
    bool      dirty       = true;        // edit-field re-render needed
    bool      keys_dirty  = true;        // full key grid re-render needed (shift toggle)
};
static KeyboardState kb;
// (LastDrawn struct below tracks per-element cached values; bg lives there.)

// ---------------------------------------------------------------------------
// UART parser.
// ---------------------------------------------------------------------------
static const char* fixName(uint8_t fix) {
    switch (fix) {
        case 0: return "NONE";
        case 1: return "DR";
        case 2: return "2D";
        case 3: return "3D";
        case 4: return "3D+DR";
        case 5: return "TIME";
        default: return "?";
    }
}
static const char* gpsStatusName(uint8_t s) {
    switch (s) {
        case 0: return "OFF";
        case 1: return "RAW";
        case 2: return "OK";
        case 3: return "STALE";
        default: return "?";
    }
}
static uint16_t gpsStatusColor(uint8_t s) {
    switch (s) {
        case 2: return TFT_GREEN;
        case 1: return TFT_YELLOW;
        case 3: return TFT_YELLOW;
        default: return TFT_RED;
    }
}

// Longest UART lines are Q,L/WUP,L upload records: "Q,L," plus one
// NDJSON sample. The Teensy-side line buffer is 320 bytes, so 256 here was
// too small and could drop perfectly valid samples mid-upload, leading to
// Teensy-side ack_timeout failures. Keep this comfortably above that.
static constexpr size_t UART_LINE_MAX = 512;
static String rxBuf;

static bool parseGpsLine(const String& line) {
    int idx[8], n = 0;
    for (int i = 0; i < (int)line.length() && n < 8; ++i) {
        if (line[i] == ',') idx[n++] = i;
    }
    if (n < 6) return false;
    idx[n] = line.length();
    auto field = [&](int k) { return line.substring(idx[k] + 1, idx[k + 1]); };
    g.fix     = (uint8_t)field(0).toInt();
    g.sats    = (uint8_t)field(1).toInt();
    g.lat_deg = field(2).toFloat();
    g.lon_deg = field(3).toFloat();
    g.mph     = field(4).toFloat();
    g.hdg_deg = field(5).toFloat();
    g.status  = (n >= 7) ? (uint8_t)field(6).toInt() : 0;
    g.last_ms = millis();
    return true;
}
static bool parseEngLine(const String& line) {
    // ENG,<rpm>[,<oil_psi_x10>,<coolant_f_x10>] — 1 OR 3 fields.
    // Older Teensy firmware (or boot before sensors stabilise) sends only
    // the rpm field; the oil/coolant values stay at -1 in that case.
    int idx[4], n = 0;
    for (int i = 0; i < (int)line.length() && n < 4; ++i)
        if (line[i] == ',') idx[n++] = i;
    if (n < 1) return false;
    idx[n] = line.length();
    auto field = [&](int k) { return line.substring(idx[k] + 1, idx[k + 1]); };

    long rpm = field(0).toInt();
    if (rpm < 0)     rpm = 0;
    if (rpm > 65535) rpm = 65535;
    eng.rpm = (uint16_t)rpm;

    if (n >= 3) {
        eng.oil_psi_x10   = (int16_t)field(1).toInt();
        eng.coolant_f_x10 = (int16_t)field(2).toInt();
    }
    eng.last_ms = millis();
    return true;
}
// Format ms into "M:SS.cs" (centiseconds), e.g. "1:23.45".
static void formatLapTime(uint32_t ms, char* buf, int bufLen) {
    const uint32_t cs = ms / 10;
    const uint32_t s  = cs / 100;
    const uint32_t m  = s  / 60;
    snprintf(buf, bufLen, "%u:%02u.%02u", (unsigned)m,
             (unsigned)(s % 60), (unsigned)(cs % 100));
}

// Wipe lap timer state; call at every recording start so times don't bleed
// across sessions. LastDrawn invalidation happens via pageJustEntered.
static void resetLapTimer() {
    lapTimer = LapTimer{};
}

// Called after every fresh GPS parse. Runs regardless of recording state —
// lap timing is based purely on GPS position vs the known S/F line for
// whatever track the car is at. START/STOP only controls data recording.
static void updateLapTimer() {
    if (g.fix < 2) return;    // no usable fix — pause, don't reset

    const int tIdx = closestTrackIdx();
    const uint32_t now = millis();

    if (tIdx < 0) {
        // Not at any known track — clear state so display shows "--:--.--".
        if (lapTimer.active) lapTimer = LapTimer{};
        return;
    }

    // First activation or track changed — initialize fresh.
    if (!lapTimer.active || lapTimer.track_idx != tIdx) {
        lapTimer              = LapTimer{};
        lapTimer.active       = true;
        lapTimer.track_idx    = tIdx;
        lapTimer.lap_start_ms = now;
        lapTimer.prev_gps_ms  = now;
        return;
    }

    // Integrate distance: speed (mph) × elapsed hours = miles.
    const float dt_h = (float)(now - lapTimer.prev_gps_ms) * (1.0f / 3600000.0f);
    lapTimer.dist_miles += g.mph * dt_h;
    lapTimer.prev_gps_ms = now;

    // Distance from THIS track's start/finish line.
    const TrackInfo& track = TRACKS[tIdx];
    const float sfKm = trackDistanceKm(g.lat_deg, g.lon_deg, track.sf_lat, track.sf_lon);
    const uint32_t elapsed = now - lapTimer.lap_start_ms;

    if (!lapTimer.left_start && sfKm > LAP_RADIUS_KM * 2.0f) {
        lapTimer.left_start = true;
    }
    if (lapTimer.left_start && sfKm <= LAP_RADIUS_KM && elapsed >= MIN_LAP_MS) {
        if (lapTimer.timing_started) {
            // Clean completed lap — record it.
            lapTimer.last_lap_ms   = elapsed;
            lapTimer.last_lap_dist = lapTimer.dist_miles;
        }
        // First crossing just arms the timer; subsequent ones record lap times.
        lapTimer.timing_started = true;
        lapTimer.lap_start_ms   = now;
        lapTimer.dist_miles     = 0.0f;
        lapTimer.left_start     = false;
        lapTimer.prev_gps_ms    = now;
    }
}

// Extrapolate a predicted final lap time. Returns 0 when there's not yet
// enough data for a meaningful estimate (< 20 % of last lap distance done).
static uint32_t predictiveLapMs() {
    if (!lapTimer.active)               return 0;
    if (lapTimer.last_lap_ms   == 0)   return 0;
    if (lapTimer.last_lap_dist < 0.001f) return 0;
    if (lapTimer.dist_miles < lapTimer.last_lap_dist * 0.20f) return 0;
    const uint32_t elapsed = millis() - lapTimer.lap_start_ms;
    const float ratio = lapTimer.last_lap_dist / lapTimer.dist_miles;
    return (uint32_t)((float)elapsed * ratio);
}

// ECU,<rpm>,<clt_f_x10>,<map_x10>,<tps_x10>,<afr_x10>,<iat_f_x10>,<bat_x10>
// Emitted by the Teensy once the MS3 CAN transceiver is wired and broadcast
// frames are decoded. Until that lands, no ECU lines arrive and the dash
// leaves ecu.* at -1, which the renderer treats as "---".
//
// All sensor fields are x10 fixed-point integers (e.g. 1450 = 14.5 AFR);
// -1 in any slot means "this field not available from MS3 right now".
static bool parseEcuLine(const String& line) {
    int idx[9], n = 0;
    for (int i = 0; i < (int)line.length() && n < 9; ++i)
        if (line[i] == ',') idx[n++] = i;
    if (n < 1) return false;
    idx[n] = line.length();
    auto field = [&](int k) { return line.substring(idx[k] + 1, idx[k + 1]); };

    long rpm = field(0).toInt();
    if (rpm < 0)     rpm = 0;
    if (rpm > 65535) rpm = 65535;
    ecu.rpm = (uint16_t)rpm;

    if (n >= 2) ecu.coolant_f_x10 = (int16_t)field(1).toInt();
    if (n >= 3) ecu.map_x10       = (int16_t)field(2).toInt();
    if (n >= 4) ecu.tps_x10       = (int16_t)field(3).toInt();
    if (n >= 5) ecu.afr_x10       = (int16_t)field(4).toInt();
    if (n >= 6) ecu.iat_f_x10     = (int16_t)field(5).toInt();
    if (n >= 7) ecu.bat_x10       = (int16_t)field(6).toInt();
    ecu.last_ms = millis();
    return true;
}

static bool parseImuLine(const String& line) {
    // IMU,<ax>,<ay>,<az>,<gx>,<gy>,<gz>
    int idx[7], n = 0;
    for (int i = 0; i < (int)line.length() && n < 7; ++i)
        if (line[i] == ',') idx[n++] = i;
    if (n < 6) return false;
    idx[n] = line.length();
    auto field = [&](int k) { return line.substring(idx[k] + 1, idx[k + 1]); };
    imu.ax = field(0).toFloat();
    imu.ay = field(1).toFloat();
    imu.az = field(2).toFloat();
    imu.gx = field(3).toFloat();
    imu.gy = field(4).toFloat();
    imu.gz = field(5).toFloat();
    imu.last_ms = millis();
    return true;
}

static bool parseEthLine(const String& line) {
    // ETH,<ip>  — sent by Teensy once DHCP assigns an address
    const int comma = line.indexOf(',');
    if (comma < 0) return false;
    const String ip = line.substring(comma + 1);
    strncpy(active_ip, ip.c_str(), sizeof(active_ip) - 1);
    active_ip[sizeof(active_ip) - 1] = '\0';
    return true;
}

static bool parseTimeLine(const String& line) {
    // TIME,<unix_epoch>  — RTC value from the Teensy, sent every 2 s
    const int comma = line.indexOf(',');
    if (comma < 0) return false;
    rtc_epoch = (uint32_t)line.substring(comma + 1).toInt();
    return true;
}

static bool parseSdLine(const String& line) {
    // SD,NONE | SD,FMT,<mb> | SD,READY,<mb>,<free_mb> | SD,ERR | SD,ACTIVE
    const int c1 = line.indexOf(',');
    if (c1 < 0) return false;
    const int c2 = line.indexOf(',', c1 + 1);
    const int c3 = (c2 >= 0) ? line.indexOf(',', c2 + 1) : -1;
    const String tag = (c2 >= 0) ? line.substring(c1 + 1, c2) : line.substring(c1 + 1);
    const uint8_t prev = sd_card_status;
    if (tag == "NONE") {
        sd_card_status = 0; sd_total_mb = 0; sd_free_mb = 0;
        // Optional 3rd field: hex error code from the Teensy SdFat probe.
        // Helps the user see *why* the card didn't mount (eg 0x14 == init
        // timeout, 0x06 == CMD8 fail). Empty when no extra info.
        if (c2 >= 0) {
            String e = line.substring(c2 + 1);
            e.trim();
            e.toCharArray(sd_err_hex, sizeof(sd_err_hex));
        } else {
            sd_err_hex[0] = '\0';
        }
    } else if (tag == "FMT") {
        sd_card_status = 1; sd_free_mb = 0;
        sd_total_mb = (c2 >= 0) ? line.substring(c2 + 1, c3 >= 0 ? c3 : (int)line.length()).toInt() : 0;
    } else if (tag == "READY") {
        sd_card_status = 2;
        sd_total_mb = (c2 >= 0) ? line.substring(c2 + 1, c3 >= 0 ? c3 : (int)line.length()).toInt() : 0;
        sd_free_mb  = (c3 >= 0) ? line.substring(c3 + 1).toInt() : 0;
        sd_err_hex[0] = '\0';   // clear stale error
    } else if (tag == "ERR") {
        sd_card_status = 3; sd_total_mb = 0; sd_free_mb = 0;
    } else if (tag == "ACTIVE") {
        sd_card_status = 4;
    } else if (tag == "REC") {
        // SD,REC,<0|1>,<filename>,<samples>
        //   c1=after SD, c2=after REC, c3=after 0|1, c4=after filename
        const int c4 = (c3 >= 0) ? line.indexOf(',', c3 + 1) : -1;
        sd_session_active = (c3 >= 0) ? (line.substring(c2 + 1, c3).toInt() != 0) : false;
        if (c3 >= 0) {
            const int end = (c4 >= 0) ? c4 : (int)line.length();
            line.substring(c3 + 1, end).toCharArray(sd_session_file, sizeof(sd_session_file));
        } else {
            sd_session_file[0] = '\0';
        }
        sd_session_samples = (c4 >= 0) ? line.substring(c4 + 1).toInt() : 0;
        return true;
    } else {
        return false;
    }
    if (sd_card_status != prev) settingsDirty = true;
    return true;
}

// Pop the modal full-screen, save the current page so we can restore it after.
static void openUploadModal(const char* filename, uint32_t total) {
    strncpy(upload_file, filename, sizeof(upload_file) - 1);
    upload_file[sizeof(upload_file) - 1] = '\0';
    upload_total       = total;
    upload_done        = 0;
    upload_active      = true;
    upload_modal_dirty = true;
    upload_result_msg[0] = '\0';
    // Only remember the return page if we weren't already showing the modal
    // (back-to-back uploads from queue drain shouldn't lose the original page).
    if (currentPage != PAGE_UPLOAD) upload_return_page = (uint8_t)currentPage;
    currentPage     = PAGE_UPLOAD;
    pageJustEntered = true;
}

// ---------------------------------------------------------------------------
// Dash-initiated upload flow (replaces the old Teensy-initiated WUP push).
//
// Flow:
//   user taps UPLOAD button on PAGE_DASH
//     -> openUploadModal('...', 0)
//     -> uf state = UF_LISTING; emit 'Q,LIST\n' to Teensy
//     -> Teensy responds: Q,FILE,<name>,<size> per file, then Q,END
//     -> for each file:
//          state = UF_FETCH_HEAD; emit 'Q,GET,<name>\n'
//          Teensy responds: Q,DATA,<name>,<size>
//            dash opens a raw TCP (or TLS) socket to s.cloud_host:port and
//            writes the HTTP request headers (Content-Length = file size).
//            state = UF_STREAMING
//          Teensy streams Q,L,<line> ... we forward each line + '\n' to the
//            open socket, incrementing bytes_written. No PSRAM staging.
//          Q,EOF arrives: verify bytes_written == expected_size for integrity,
//            flush socket, state = UF_STREAM_FINISH
//        uploadTick drains the response progressively, parses HTTP status
//          on 2xx: emit 'Q,DEL,<name>\n'; state = UF_DELETING
//          on fail: skip; advance to next file (file stays on SD)
//        on Q,DEL,OK: advance to next file
//     -> when all files processed: state = UF_DONE; show summary banner
// ---------------------------------------------------------------------------
struct UfPendingFile {
    char     name[80];
    uint32_t size;
};

struct UploadFlow {
    UploadFlowState state;
    uint32_t state_entered_ms;
    UfPendingFile files[16];
    int      files_n;
    int      files_idx;
    int      uploaded;
    int      failed;
    // Streaming TCP socket. Owned. Polymorphic across WiFiClient (HTTP) and
    // WiFiClientSecure (HTTPS); deleted via base virtual destructor.
    WiFiClient* tcp;
    bool       tcp_secure;
    uint32_t   expected_size;   // Content-Length value (from Q,DATA)
    uint32_t   bytes_written;   // bytes written to socket so far (line + '\n' per Q,L)
    uint32_t   lines_recv;      // Q,L count for current file (debug + DBG progress)
    uint32_t   last_rx_ms;      // most recent UART or socket activity (for stall watchdog)
    char       response[1024];  // accumulated HTTP response (headers + body)
    size_t     response_len;
    char       last_err[180];
};
static UploadFlow uf = {};

static void ufCloseTcp() {
    if (uf.tcp) {
        uf.tcp->stop();
        delete uf.tcp;
        uf.tcp = nullptr;
    }
    uf.tcp_secure   = false;
    uf.expected_size = 0;
    uf.bytes_written = 0;
    uf.lines_recv   = 0;
    uf.response_len = 0;
    uf.response[0]  = '\0';
}

static void ufReset() {
    ufCloseTcp();
    memset(&uf, 0, sizeof(uf));
    uf.state = UF_IDLE;
}

static void ufEnter(UploadFlowState s) {
    uf.state = s;
    uf.state_entered_ms = millis();
    uf.last_rx_ms       = millis();
}

static void ufStartListing() {
    ufReset();
    ufEnter(UF_LISTING);
    Serial.println("Q,LIST");
    Serial.flush();
}

static void ufStartCurrentFile() {
    if (uf.files_idx >= uf.files_n) {
        ufEnter(UF_DONE);
        return;
    }
    Serial.printf("Q,GET,%s\n", uf.files[uf.files_idx].name);
    Serial.flush();
    ufEnter(UF_FETCH_HEAD);
}

static void ufNextFile() {
    ufCloseTcp();
    uf.files_idx++;
    ufStartCurrentFile();
}

// Parse the unix-epoch session id out of a 'session_<epoch>_<track>.ndjson'
// filename; falls back to millis() when the filename doesn't match.
static long ufExtractSessionId(const char* filename) {
    if (filename && strncmp(filename, "session_", 8) == 0) {
        const long v = strtol(filename + 8, nullptr, 10);
        if (v > 0) return v;
    }
    return (long)millis();
}

// Open the TCP/TLS socket to the cloud and write the HTTP request headers.
// Body bytes are written incrementally as Q,L lines arrive. Returns true on
// success; on failure, last_err is set and the caller should advance to the
// next file.
static bool ufOpenStream(uint32_t content_length) {
    if (s.cloud_host[0] == '\0' || s.cloud_port == 0) {
        snprintf(uf.last_err, sizeof(uf.last_err), "cloud host/port unset");
        return false;
    }
    if (s.internet_mode != 1 || !wifiConnectedNow()) {
        snprintf(uf.last_err, sizeof(uf.last_err), "WiFi not connected");
        return false;
    }
    ufCloseTcp();
    // Tighter than the Teensy's 10 s per-line ACK wait, so a stalled TCP
    // write fails fast on this side instead of hanging long enough for the
    // Teensy to give up and abort the whole transfer with Q,ERR,ack_timeout.
    constexpr int CLOUD_TCP_TIMEOUT_S = 8;
    if (s.cloud_protocol == 1) {
        WiFiClientSecure* sec = new WiFiClientSecure();
        sec->setInsecure();   // TODO: pin server cert when going public
        sec->setTimeout(CLOUD_TCP_TIMEOUT_S);
        uf.tcp = sec;
        uf.tcp_secure = true;
    } else {
        WiFiClient* plain = new WiFiClient();
        plain->setTimeout(CLOUD_TCP_TIMEOUT_S);
        uf.tcp = plain;
        uf.tcp_secure = false;
    }
    Serial.printf("DBG,uf_connect host=%s port=%u sec=%d size=%lu\n",
                  s.cloud_host, (unsigned)s.cloud_port, (int)uf.tcp_secure,
                  (unsigned long)content_length);
    if (!uf.tcp->connect(s.cloud_host, s.cloud_port)) {
        snprintf(uf.last_err, sizeof(uf.last_err), "TCP connect failed");
        ufCloseTcp();
        return false;
    }
    // Disable Nagle so per-line writes go out immediately rather than waiting
    // for the TCP coalescer. The Teensy is paced by Q,A acks anyway, so we
    // never benefit from coalescing and Nagle just adds latency to each ACK
    // round trip — which directly slows the upload.
    uf.tcp->setNoDelay(true);
    const long sid = ufExtractSessionId(uf.files[uf.files_idx].name);
    uf.tcp->printf("POST /upload HTTP/1.1\r\n");
    uf.tcp->printf("Host: %s\r\n",            s.cloud_host);
    uf.tcp->printf("Content-Type: application/x-ndjson\r\n");
    uf.tcp->printf("Content-Length: %lu\r\n", (unsigned long)content_length);
    uf.tcp->printf("X-API-Key: %s\r\n",       s.cloud_auth_pass);
    uf.tcp->printf("X-User-Email: %s\r\n",    s.cloud_auth_user);
    uf.tcp->printf("X-Session-Id: %ld\r\n",   sid);
    uf.tcp->printf("X-Track-Name: %s\r\n",    uf.files[uf.files_idx].name);
    uf.tcp->printf("Connection: close\r\n");
    uf.tcp->printf("\r\n");
    uf.expected_size = content_length;
    uf.bytes_written = 0;
    uf.lines_recv    = 0;
    uf.response_len  = 0;
    return true;
}

// ---------------------------------------------------------------------------
// PAGE_SESSIONS state. Reuses the same Q,LIST / Q,DEL wire protocol that the
// upload flow uses but keeps its own data so the user can still tap UPLOAD
// on PAGE_DASH while browsing the queue here. The SessionsListState enum is
// forward-declared at the top of the file (see uploads section) so the auto
// prototyper can see slEnter(SessionsListState) signatures.
// ---------------------------------------------------------------------------
static constexpr int SESSIONS_MAX_FILES = 24;   // bounded to keep RAM use predictable

struct SessionsList {
    SessionsListState state;
    uint32_t state_entered_ms;
    char     files[SESSIONS_MAX_FILES][80];
    uint32_t sizes[SESSIONS_MAX_FILES];
    bool     selected[SESSIONS_MAX_FILES];
    int      count;
    // Delete batch progress.
    int      del_idx;       // currently-being-deleted index in files[]
    int      del_done;      // total OKs in this batch
    int      del_fail;      // total fails in this batch
    char     last_err[64];
    bool     delete_all_mode;
    bool     dirty;
};
static SessionsList sl = {};
static int sessions_scroll_y = 0;

static void slReset() {
    memset(&sl, 0, sizeof(sl));
    sl.state = SL_IDLE;
    sessions_scroll_y = 0;
}

static void slEnter(SessionsListState st) {
    sl.state = st;
    sl.state_entered_ms = millis();
    sl.dirty = true;
}

static void sessionsRequestList() {
    slReset();
    slEnter(SL_LISTING);
    Serial.println("Q,LIST");
    Serial.flush();
}

// Walk sl.files looking for the next selected file (or any file in delete-all
// mode). Returns the index, or -1 if there are none left to delete.
static int sl_next_to_delete(int from_idx) {
    for (int i = from_idx; i < sl.count; ++i) {
        if (sl.delete_all_mode || sl.selected[i]) return i;
    }
    return -1;
}

static void slStartDelete(bool delete_all) {
    if (sl.state == SL_DELETING) return;       // already running
    if (sl.count == 0) return;
    sl.delete_all_mode = delete_all;
    sl.del_done = sl.del_fail = 0;
    sl.last_err[0] = '\0';
    sl.del_idx = sl_next_to_delete(0);
    if (sl.del_idx < 0) return;                // nothing selected
    slEnter(SL_DELETING);
    Serial.printf("Q,DEL,%s\n", sl.files[sl.del_idx]);
    Serial.flush();
}

static bool parseQLine(const String& line) {
    // Q,FILE,<name>,<size>
    // Q,END[,<reason>]
    // Q,DATA,<name>,<size>
    // Q,L,<ndjson>
    // Q,EOF,<line_count>
    // Q,ERR,<reason>
    // Q,DEL,OK | Q,DEL,FAIL,<reason>
    const char* p = line.c_str() + 2;   // skip 'Q,'

    // PAGE_SESSIONS consumer (preferred when it's actively listing/deleting).
    if (strncmp(p, "FILE,", 5) == 0 && sl.state == SL_LISTING) {
        const char* rest = p + 5;
        const char* comma = strchr(rest, ',');
        if (!comma || sl.count >= SESSIONS_MAX_FILES) return true;
        const size_t name_len = (size_t)(comma - rest);
        if (name_len >= sizeof(sl.files[0])) return true;
        memcpy(sl.files[sl.count], rest, name_len);
        sl.files[sl.count][name_len] = '\0';
        sl.sizes[sl.count] = (uint32_t)strtoul(comma + 1, nullptr, 10);
        sl.selected[sl.count] = false;
        sl.count++;
        sl.dirty = true;
        return true;
    }
    if (strncmp(p, "END", 3) == 0 && sl.state == SL_LISTING) {
        slEnter(SL_IDLE);
        return true;
    }
    if (strncmp(p, "DEL,", 4) == 0 && sl.state == SL_DELETING) {
        if (strncmp(p + 4, "OK", 2) == 0) sl.del_done++;
        else {
            sl.del_fail++;
            snprintf(sl.last_err, sizeof(sl.last_err), "%s", p + 4);
        }
        // advance to next file to delete
        const int next = sl_next_to_delete(sl.del_idx + 1);
        if (next < 0) {
            // Done; refresh list to drop the deleted entries.
            sessionsRequestList();
        } else {
            sl.del_idx = next;
            Serial.printf("Q,DEL,%s\n", sl.files[sl.del_idx]);
            Serial.flush();
            sl.state_entered_ms = millis();
        }
        return true;
    }

    // Upload-flow consumer.
    if (strncmp(p, "FILE,", 5) == 0 && uf.state == UF_LISTING) {
        const char* rest = p + 5;
        const char* comma = strchr(rest, ',');
        if (!comma || uf.files_n >= (int)(sizeof(uf.files)/sizeof(uf.files[0]))) return true;
        const size_t name_len = (size_t)(comma - rest);
        if (name_len >= sizeof(uf.files[0].name)) return true;
        memcpy(uf.files[uf.files_n].name, rest, name_len);
        uf.files[uf.files_n].name[name_len] = '\0';
        uf.files[uf.files_n].size = (uint32_t)strtoul(comma + 1, nullptr, 10);
        uf.files_n++;
        return true;
    }
    if (strncmp(p, "END", 3) == 0 && uf.state == UF_LISTING) {
        if (uf.files_n == 0) {
            ufEnter(UF_DONE);
        } else {
            ufStartCurrentFile();
        }
        return true;
    }
    if (strncmp(p, "DATA,", 5) == 0 && uf.state == UF_FETCH_HEAD) {
        const char* rest = p + 5;
        const char* comma = strchr(rest, ',');
        if (!comma) return true;
        const uint32_t sz = (uint32_t)strtoul(comma + 1, nullptr, 10);
        // Open the cloud socket NOW and write the HTTP headers. Body bytes
        // will be written line-by-line as Q,L messages arrive (no PSRAM
        // buffer); the server reads exactly Content-Length=sz body bytes.
        if (!ufOpenStream(sz)) {
            uf.failed++;
            ufNextFile();
            return true;
        }
        ufEnter(UF_STREAMING);
        return true;
    }
    if (strncmp(p, "L,", 2) == 0 && uf.state == UF_STREAMING) {
        const char* data = p + 2;
        const size_t n = strlen(data);
        if (!uf.tcp || !uf.tcp->connected()) {
            snprintf(uf.last_err, sizeof(uf.last_err),
                     "TCP died at %lu bytes", (unsigned long)uf.bytes_written);
            ufCloseTcp();
            uf.failed++;
            ufNextFile();
            return true;
        }
        // Single write per line: stack-build "<line>\n" then write once.
        // Two writes per line through WiFiClientSecure adds an extra TLS
        // record header per line — over 4000 lines on a 1 MB upload that's
        // a measurable overhead and an extra blocking syscall per line.
        uint8_t tx[576];
        if (n + 1 > sizeof(tx)) {
            snprintf(uf.last_err, sizeof(uf.last_err),
                     "line too long %u", (unsigned)n);
            ufCloseTcp();
            uf.failed++;
            ufNextFile();
            return true;
        }
        memcpy(tx, data, n);
        tx[n] = '\n';
        const size_t need = n + 1;
        const size_t w = uf.tcp->write(tx, need);
        if (w != need) {
            snprintf(uf.last_err, sizeof(uf.last_err),
                     "TCP short write %u/%u at %lu B",
                     (unsigned)w, (unsigned)need,
                     (unsigned long)uf.bytes_written);
            ufCloseTcp();
            uf.failed++;
            ufNextFile();
            return true;
        }
        uf.bytes_written += need;
        uf.last_rx_ms     = millis();
        uf.lines_recv++;

        // Pace the Teensy file sender. It waits for Q,A after every Q,L line;
        // without this ACK, uploads fail as Q,ERR,ack_timeout as soon as the
        // first data record is sent. ACK only after the bytes are accepted by
        // the cloud socket so TCP backpressure naturally slows the SD reader.
        Serial.println("Q,A");
        Serial.flush();

        if ((uf.lines_recv % 500) == 0) {
            Serial.printf("DBG,uf_stream lines=%lu bytes=%lu/%lu\n",
                          (unsigned long)uf.lines_recv,
                          (unsigned long)uf.bytes_written,
                          (unsigned long)uf.expected_size);
        }
        return true;
    }
    if (strncmp(p, "EOF", 3) == 0 && uf.state == UF_STREAMING) {
        if (!uf.tcp) {
            snprintf(uf.last_err, sizeof(uf.last_err), "no tcp at EOF");
            uf.failed++;
            ufNextFile();
            return true;
        }
        if (uf.bytes_written != uf.expected_size) {
            // Server is waiting for exactly Content-Length bytes. Anything
            // less is a data integrity failure: lines dropped, the file got
            // truncated mid-stream, etc.
            Serial.printf("DBG,uf_eof_short wrote=%lu expected=%lu lines=%lu\n",
                          (unsigned long)uf.bytes_written,
                          (unsigned long)uf.expected_size,
                          (unsigned long)uf.lines_recv);
            snprintf(uf.last_err, sizeof(uf.last_err),
                     "stream short: %lu/%lu B",
                     (unsigned long)uf.bytes_written,
                     (unsigned long)uf.expected_size);
            ufCloseTcp();
            uf.failed++;
            ufNextFile();
            return true;
        }
        uf.tcp->flush();
        Serial.printf("DBG,uf_eof_ok wrote=%lu lines=%lu\n",
                      (unsigned long)uf.bytes_written,
                      (unsigned long)uf.lines_recv);
        ufEnter(UF_STREAM_FINISH);
        return true;
    }
    if (strncmp(p, "ERR,", 4) == 0) {
        snprintf(uf.last_err, sizeof(uf.last_err), "%s", p + 4);
        uf.failed++;
        ufNextFile();
        return true;
    }
    if (strncmp(p, "DEL,", 4) == 0 && uf.state == UF_DELETING) {
        if (strncmp(p + 4, "OK", 2) == 0) {
            uf.uploaded++;
        } else {
            snprintf(uf.last_err, sizeof(uf.last_err), "DEL: %s", p + 4);
        }
        ufNextFile();
        return true;
    }
    return false;
}

// Parse the accumulated HTTP response in uf.response and return the status
// code. body_snip is filled with a one-line snippet of the response body for
// display in the modal banner. Returns 0 if no parseable status line.
static int ufParseResponse(char* body_snip, size_t body_snip_sz) {
    body_snip[0] = '\0';
    if (uf.response_len == 0) return 0;
    int code = 0;
    const char* sp = strchr(uf.response, ' ');
    if (sp) code = atoi(sp + 1);
    const char* bs = strstr(uf.response, "\r\n\r\n");
    const char* body = bs ? bs + 4 : "";
    // Strip CR/LF for display; collapse runs of whitespace into single spaces.
    size_t k = 0;
    bool   prev_space = false;
    for (size_t i = 0; body[i] && k < body_snip_sz - 1; ++i) {
        const char c = body[i];
        if (c == '\n' || c == '\r' || c == '\t' || c == ' ') {
            if (!prev_space && k > 0) {
                body_snip[k++] = ' ';
                prev_space = true;
            }
        } else {
            body_snip[k++] = c;
            prev_space = false;
        }
    }
    body_snip[k] = '\0';
    return code;
}

static void uploadTick() {
    if (uf.state == UF_IDLE) return;
    const uint32_t now = millis();

    // Drive modal display whenever state has moved.
    if (upload_active) {
        char fname[80] = "";
        uint32_t total = 1, done = 0;
        if (uf.files_idx < uf.files_n) {
            snprintf(fname, sizeof(fname), "%s", uf.files[uf.files_idx].name);
            total = uf.expected_size > 0 ? uf.expected_size
                                          : uf.files[uf.files_idx].size > 0
                                              ? uf.files[uf.files_idx].size
                                              : 1;
            done  = uf.bytes_written;
        }
        if (strcmp(upload_file, fname) != 0 ||
            total != upload_total || done != upload_done) {
            strncpy(upload_file, fname, sizeof(upload_file) - 1);
            upload_file[sizeof(upload_file) - 1] = '\0';
            upload_total = total;
            upload_done  = done;
            upload_modal_dirty = true;
        }
    }

    // Per-state housekeeping.
    if (uf.state == UF_STREAM_FINISH) {
        if (!uf.tcp) {
            snprintf(uf.last_err, sizeof(uf.last_err), "no tcp in finish");
            uf.failed++;
            ufNextFile();
            return;
        }
        // Drain any available HTTP response bytes into our buffer.
        while (uf.tcp->available()) {
            const int c = uf.tcp->read();
            if (c < 0) break;
            if (uf.response_len + 1 < sizeof(uf.response)) {
                uf.response[uf.response_len++] = (char)c;
                uf.response[uf.response_len]   = '\0';
            }
            uf.last_rx_ms = millis();
        }
        // We only need the HTTP status. Do not require the server to close the
        // socket: some HTTP/1.1 stacks keep it open even when we ask for
        // Connection: close, which made otherwise-complete uploads look like
        // response timeouts. Parse as soon as response headers are complete;
        // otherwise fall back to parsing after disconnect.
        const bool headers_complete = (strstr(uf.response, "\r\n\r\n") != nullptr);
        const bool socket_done = (!uf.tcp->connected() && !uf.tcp->available());
        if (headers_complete || socket_done) {
            char body[140];
            const int code = ufParseResponse(body, sizeof(body));
            Serial.printf("DBG,uf_response code=%d body=%s\n", code, body);
            ufCloseTcp();
            if (code >= 200 && code < 300) {
                Serial.printf("Q,DEL,%s\n", uf.files[uf.files_idx].name);
                Serial.flush();
                ufEnter(UF_DELETING);
            } else {
                if (code > 0 && body[0]) {
                    snprintf(uf.last_err, sizeof(uf.last_err),
                             "http %d: %s", code, body);
                } else if (code > 0) {
                    snprintf(uf.last_err, sizeof(uf.last_err), "http %d", code);
                } else {
                    snprintf(uf.last_err, sizeof(uf.last_err), "no http response");
                }
                uf.failed++;
                ufNextFile();
            }
        }
        return;
    }
    if (uf.state == UF_DONE) {
        // Build summary banner once.
        if (upload_result_msg[0] == '\0') {
            if (uf.failed == 0 && uf.uploaded > 0) {
                snprintf(upload_result_msg, sizeof(upload_result_msg),
                         "OK: %d uploaded", uf.uploaded);
            } else if (uf.uploaded == 0 && uf.failed > 0) {
                snprintf(upload_result_msg, sizeof(upload_result_msg),
                         "FAIL: %s", uf.last_err[0] ? uf.last_err : "all uploads failed");
            } else if (uf.failed > 0) {
                snprintf(upload_result_msg, sizeof(upload_result_msg),
                         "OK: %d up, %d failed", uf.uploaded, uf.failed);
            } else {
                snprintf(upload_result_msg, sizeof(upload_result_msg), "OK: empty queue");
            }
            upload_modal_dirty  = true;
            upload_last_draw_ms = now;
        }
        return;
    }

    // Timeout watchdogs. For wait-for-first-response states the clock starts
    // when we entered the state. For UF_STREAMING and UF_STREAM_FINISH the
    // clock is activity-based: we only fail if there's a sustained stall
    // (last_rx_ms aged out), so a slow but progressing transfer succeeds.
    uint32_t timeout_ms = 0;
    uint32_t since      = 0;
    switch (uf.state) {
        case UF_LISTING:        timeout_ms = 6000;   since = now - uf.state_entered_ms; break;
        case UF_FETCH_HEAD:     timeout_ms = 6000;   since = now - uf.state_entered_ms; break;
        case UF_STREAMING:      timeout_ms = 20000;  since = now - uf.last_rx_ms;       break;
        case UF_STREAM_FINISH:  timeout_ms = 30000;  since = now - uf.last_rx_ms;       break;
        case UF_DELETING:       timeout_ms = 6000;   since = now - uf.state_entered_ms; break;
        default: return;
    }
    if (since > timeout_ms) {
        if (uf.state == UF_STREAMING) {
            snprintf(uf.last_err, sizeof(uf.last_err),
                     "stalled at %lu/%lu B (no data for %lus)",
                     (unsigned long)uf.bytes_written,
                     (unsigned long)uf.expected_size,
                     (unsigned long)(since / 1000));
        } else if (uf.state == UF_STREAM_FINISH) {
            snprintf(uf.last_err, sizeof(uf.last_err),
                     "no server response in %lus", (unsigned long)(since / 1000));
        } else {
            snprintf(uf.last_err, sizeof(uf.last_err),
                     "timeout in state %u after %lus",
                     (unsigned)uf.state, (unsigned long)(since / 1000));
        }
        Serial.printf("DBG,uf_timeout state=%u %s\n",
                      (unsigned)uf.state, uf.last_err);
        ufCloseTcp();
        if (uf.state == UF_LISTING) ufEnter(UF_DONE);
        else { uf.failed++; ufNextFile(); }
    }
}

static void closeUploadModal() {
    upload_active      = false;
    upload_result_msg[0] = '\0';
    currentPage        = (Page)upload_return_page;
    pageJustEntered    = true;
    settingsDirty      = true;
    invalidateAll();
    ufReset();   // ensure UPLOAD button next tap starts a fresh flow
}

static bool parseVerLine(const String& line) {
    // VER,<who>,<version>   e.g. "VER,teensy,0.1.0"
    const int c1 = line.indexOf(',');
    if (c1 < 0) return false;
    const int c2 = line.indexOf(',', c1 + 1);
    if (c2 < 0) return false;
    const String who = line.substring(c1 + 1, c2);
    const String ver = line.substring(c2 + 1);
    if (who == "teensy") {
        ver.toCharArray(teensy_fw_version, sizeof(teensy_fw_version));
        // NOTE: do NOT Serial.printf() here — Serial is UART0 which goes back
        // to the Teensy. Any diagnostic would round-trip and the Teensy would
        // log it as 'unknown dash cmd'. If we ever add a separate USB CDC for
        // dash diagnostics, log it there instead.
    }
    return true;
}

static bool parseUploadLine(const String& line) {
    // UPLOAD,START,<filename>,<total_bytes>
    // UPLOAD,PROG,<bytes_done>
    // UPLOAD,DONE,<OK|FAIL|CANCELLED>
    const int c1 = line.indexOf(',');
    if (c1 < 0) return false;
    const int c2 = line.indexOf(',', c1 + 1);
    const String tag = (c2 >= 0) ? line.substring(c1 + 1, c2) : line.substring(c1 + 1);
    if (tag == "START") {
        const int c3 = (c2 >= 0) ? line.indexOf(',', c2 + 1) : -1;
        if (c3 < 0) return false;
        const String fn = line.substring(c2 + 1, c3);
        const uint32_t total = (uint32_t)line.substring(c3 + 1).toInt();
        char fnBuf[64]; fn.toCharArray(fnBuf, sizeof(fnBuf));
        openUploadModal(fnBuf, total);
        return true;
    }
    if (tag == "PROG") {
        if (c2 < 0) return false;
        upload_done        = (uint32_t)line.substring(c2 + 1).toInt();
        upload_modal_dirty = true;
        return true;
    }
    if (tag == "DONE") {
        const String status = (c2 >= 0) ? line.substring(c2 + 1) : String("OK");
        // Hold the modal up for 800 ms with a status banner so the user
        // sees the outcome rather than a flash-and-gone.
        snprintf(upload_result_msg, sizeof(upload_result_msg), "%s", status.c_str());
        upload_modal_dirty  = true;
        upload_last_draw_ms = millis();   // start the post-DONE timer
        upload_done         = upload_total;
        return true;
    }
    return false;
}

static bool parseCldLine(const String& line) {
    // CLD,<live_ok>,<queue_depth>
    const int c1 = line.indexOf(',');
    const int c2 = (c1 >= 0) ? line.indexOf(',', c1 + 1) : -1;
    if (c1 < 0 || c2 < 0) return false;
    cloud_live_ok     = (line.substring(c1 + 1, c2).toInt() != 0);
    cloud_queue_depth = (uint32_t)line.substring(c2 + 1).toInt();
    return true;
}

// Local mirror of the Teensy test_mode_active flag. Updated by TEST,<0|1>
// lines so the Tools page button shows the correct label even across reboots.
static bool test_mode_active = false;
static bool parseTestLine(const String& line) {
    // TEST,<0|1>
    const int c1 = line.indexOf(',');
    if (c1 < 0) return false;
    test_mode_active = (line.substring(c1 + 1).toInt() != 0);
    return true;
}

// parseWupLine() is defined far below — it touches wifi_state which lives in
// the WiFi section. Just a forward decl up here so parseLine() can dispatch
// to it from this top-of-file UART parsing block.
static bool parseWupLine(const String& line);

static bool parseLine(const String& line) {
    if (line.startsWith("GPS,")) {
        const bool ok = parseGpsLine(line);
        if (ok) updateLapTimer();
        return ok;
    }
    if (line.startsWith("ENG,")) return parseEngLine(line);
    if (line.startsWith("ECU,")) return parseEcuLine(line);
    if (line.startsWith("IMU,")) return parseImuLine(line);
    if (line.startsWith("ETH,"))  return parseEthLine(line);
    if (line.startsWith("SD,"))   return parseSdLine(line);
    if (line.startsWith("CLD,"))  return parseCldLine(line);
    if (line.startsWith("TIME,")) return parseTimeLine(line);
    if (line.startsWith("UPLOAD,")) return parseUploadLine(line);
    if (line.startsWith("VER,"))    return parseVerLine(line);
    if (line.startsWith("TEST,"))   return parseTestLine(line);
    if (line.startsWith("WUP,"))    return parseWupLine(line);
    if (line.startsWith("Q,"))     return parseQLine(line);
    return false;
}
static void pumpUart() {
    while (Serial.available()) {
        char c = (char)Serial.read();
        if (c == '\r') continue;
        if (c == '\n') { parseLine(rxBuf); rxBuf = ""; }
        else if (rxBuf.length() < UART_LINE_MAX) { rxBuf += c; }
        else { rxBuf = ""; }
    }
}

// ---------------------------------------------------------------------------
// Touch handling — swipe detection + tap dispatch.
// Tracks touch start/end, classifies into tap or horizontal swipe on release.
// ---------------------------------------------------------------------------
// Settings page can grow taller than the screen — drag-to-scroll via finger.
// Header and footer are sticky; only the row band scrolls.
static int  settingsScrollY = 0;
static int  settingsContentHeight = 0;       // computed in drawSettingsPage()
static void clampSettingsScroll();

enum Gesture : uint8_t {
    GESTURE_NONE = 0,             // not yet classified
    GESTURE_DRAG_V,               // active vertical drag (settings scroll)
    GESTURE_SWIPE_H,              // tentative horizontal swipe — confirmed on release
};

struct TouchTracker {
    bool     active           = false;
    int32_t  startX           = 0;
    int32_t  startY           = 0;
    int32_t  lastX            = 0;
    int32_t  lastY            = 0;
    uint32_t startMs          = 0;
    Gesture  gesture          = GESTURE_NONE;
    int      scrollAtStart    = 0;
};
static TouchTracker tt;

constexpr int  SWIPE_DX_MIN     = 120;
constexpr int  SWIPE_DY_MAX     = 100;
constexpr uint32_t SWIPE_MS_MAX = 800;
constexpr int  TAP_DXY_MAX      = 30;
constexpr uint32_t TAP_MS_MAX   = 600;
constexpr int  GESTURE_THRESH   = 30;        // movement before we classify

// Forward decls.
static void handleSettingsTap(int x, int y);
static void handleDashTap(int x, int y);
static void handleTimeSetTap(int x, int y);
static void openTrackPicker(bool for_recording = false);
static void openConfigPicker(int track_idx, bool from_auto, bool for_recording = false);
static void handleConfigPickerTap(int x, int y);
static void handleWifiScannerTap(int x, int y);
static void drawWifiScannerPage();
static void drawUploadModal();
static void handleUploadModalTap(int x, int y);
static bool parseUploadLine(const String& line);
static bool parseQLine(const String& line);
static void ufStartListing();
static void uploadTick();
static void handleSessionsTap(int x, int y);
static void drawSessionsPage();
static void sessionsRequestList();
static void drawOtaModal();
static void handleOtaModalTap(int x, int y);
static void otaTick();
static void otaStart();
static void drawToolsPage();
static void handleToolsTap(int x, int y);
static bool parseVerLine(const String& line);
static void handleStatusTap(int x, int y);

static void handleTouch() {
    int32_t x, y;
    const bool now = tft.getTouch(&x, &y);

    // Keyboard + track picker pages use a tap-only model (with vertical
    // drag for picker scrolling). No swipe-back; CANCEL is the way out.
    // While an upload is active the modal owns the screen — only its CANCEL
    // button accepts input. Drop every other touch event.
    if (currentPage == PAGE_UPLOAD) {
        if (now && !tt.active) {
            tt.startX = x; tt.startY = y;
            tt.lastX  = x; tt.lastY  = y;
            tt.startMs = millis();
            tt.active  = true;
        } else if (!now && tt.active) {
            handleUploadModalTap(tt.startX, tt.startY);
            tt.active = false;
        }
        return;
    }
    // OTA modal: same as upload — only buttons on the modal are tappable.
    if (currentPage == PAGE_OTA) {
        if (now && !tt.active) {
            tt.startX = x; tt.startY = y;
            tt.lastX  = x; tt.lastY  = y;
            tt.startMs = millis();
            tt.active  = true;
        } else if (!now && tt.active) {
            handleOtaModalTap(tt.startX, tt.startY);
            tt.active = false;
        }
        return;
    }
    if (currentPage == PAGE_NUM_KB || currentPage == PAGE_TEXT_KB ||
        currentPage == PAGE_CONFIG_PICKER || currentPage == PAGE_TIME_SET ||
        currentPage == PAGE_WIFI_SCAN) {
        if (now && !tt.active) {
            tt.startX = x; tt.startY = y;
            tt.lastX  = x; tt.lastY  = y;
            tt.startMs = millis();
            tt.active  = true;
        } else if (!now && tt.active) {
            if      (currentPage == PAGE_CONFIG_PICKER) handleConfigPickerTap(tt.startX, tt.startY);
            else if (currentPage == PAGE_TIME_SET)      handleTimeSetTap(tt.startX, tt.startY);
            else if (currentPage == PAGE_WIFI_SCAN)     handleWifiScannerTap(tt.startX, tt.startY);
            else                                        handleKeyboardTap(tt.startX, tt.startY);
            tt.active = false;
        } else if (now && tt.active) {
            tt.lastX = x; tt.lastY = y;
        }
        return;
    }
    if (currentPage == PAGE_TRACK_PICKER) {
        if (now && !tt.active) {
            tt.startX = x; tt.startY = y;
            tt.lastX  = x; tt.lastY  = y;
            tt.startMs = millis();
            tt.active  = true;
            tt.gesture = GESTURE_NONE;
            tt.scrollAtStart = tp.scrollY;
        } else if (now && tt.active) {
            const int dx = x - tt.startX;
            const int dy = y - tt.startY;
            if (tt.gesture == GESTURE_NONE
                && (abs(dx) > GESTURE_THRESH || abs(dy) > GESTURE_THRESH)) {
                tt.gesture = (abs(dy) > abs(dx)) ? GESTURE_DRAG_V : GESTURE_SWIPE_H;
            }
            if (tt.gesture == GESTURE_DRAG_V) {
                tp.scrollY = tt.scrollAtStart - dy;
                clampPickerScroll();
                tp.dirty = true;
            }
            tt.lastX = x; tt.lastY = y;
        } else if (!now && tt.active) {
            if (tt.gesture == GESTURE_NONE) {
                handleTrackPickerTap(tt.startX, tt.startY);
            }
            tt.active = false;
        }
        return;
    }

    if (now && !tt.active) {
        // ---- Touch start ----
        tt.startX = x; tt.startY = y;
        tt.lastX  = x; tt.lastY  = y;
        tt.startMs = millis();
        tt.active  = true;
        tt.gesture = GESTURE_NONE;
        tt.scrollAtStart = settingsScrollY;
        return;
    }

    if (now && tt.active) {
        // ---- Touch dragging ----
        const int dxFromStart = x - tt.startX;
        const int dyFromStart = y - tt.startY;

        // Classify on first significant movement.
        if (tt.gesture == GESTURE_NONE
            && (abs(dxFromStart) > GESTURE_THRESH || abs(dyFromStart) > GESTURE_THRESH)) {
            if (currentPage == PAGE_SETTINGS && abs(dyFromStart) > abs(dxFromStart)) {
                tt.gesture = GESTURE_DRAG_V;
            } else {
                tt.gesture = GESTURE_SWIPE_H;
            }
        }

        if (tt.gesture == GESTURE_DRAG_V) {
            settingsScrollY = tt.scrollAtStart - dyFromStart;
            clampSettingsScroll();
            settingsDirty = true;
        }

        tt.lastX = x; tt.lastY = y;
        return;
    }

    if (!now && tt.active) {
        // ---- Touch release ----
        const int      dx  = tt.lastX - tt.startX;
        const int      dy  = tt.lastY - tt.startY;
        const uint32_t dur = millis() - tt.startMs;

        if (tt.gesture == GESTURE_DRAG_V) {
            // Already handled per-frame; nothing else to do.
        } else if (tt.gesture == GESTURE_SWIPE_H) {
            if (abs(dx) > SWIPE_DX_MIN && abs(dy) < SWIPE_DY_MAX && dur < SWIPE_MS_MAX) {
                if (dx < 0 && currentPage == PAGE_DASH) {
                    currentPage = PAGE_SETTINGS;
                    pageJustEntered = true;
                } else if (dx > 0 && currentPage == PAGE_SETTINGS) {
                    saveSettings();
                    currentPage = PAGE_DASH;
                    pageJustEntered = true;
                } else if (dx < 0 && currentPage == PAGE_SETTINGS) {
                    saveSettings();
                    currentPage = PAGE_STATUS;
                    pageJustEntered = true;
                } else if (dx > 0 && currentPage == PAGE_STATUS) {
                    currentPage = PAGE_SETTINGS;
                    pageJustEntered = true;
                    settingsDirty = true;
                } else if (dx < 0 && currentPage == PAGE_STATUS) {
                    currentPage = PAGE_TOOLS;
                    pageJustEntered = true;
                } else if (dx > 0 && currentPage == PAGE_TOOLS) {
                    currentPage = PAGE_STATUS;
                    pageJustEntered = true;
                } else if (dx < 0 && currentPage == PAGE_TOOLS) {
                    currentPage = PAGE_SESSIONS;
                    pageJustEntered = true;
                } else if (dx > 0 && currentPage == PAGE_SESSIONS) {
                    currentPage = PAGE_TOOLS;
                    pageJustEntered = true;
                }
            }
        } else {  // GESTURE_NONE — never moved much, treat as tap
            if (abs(dx) < TAP_DXY_MAX && abs(dy) < TAP_DXY_MAX && dur < TAP_MS_MAX) {
                if (currentPage == PAGE_DASH)          handleDashTap(tt.startX, tt.startY);
                else if (currentPage == PAGE_SETTINGS) handleSettingsTap(tt.startX, tt.startY);
                else if (currentPage == PAGE_TOOLS)    handleToolsTap(tt.startX, tt.startY);
                else if (currentPage == PAGE_STATUS)   handleStatusTap(tt.startX, tt.startY);
                else if (currentPage == PAGE_SESSIONS) handleSessionsTap(tt.startX, tt.startY);
            }
        }
        tt.active = false;
    }
}

static void handleDashTap(int x, int y) {
    // TRACK button — opens picker in select-only mode (no recording start).
    if (x >= TRKBTN_X && x < TRKBTN_X + TRKBTN_W &&
        y >= TRKBTN_Y && y < TRKBTN_Y + TRKBTN_H) {
        openTrackPicker(false);
        return;
    }

    // Manual UPLOAD button (only acts when visible: idle + queue > 0).
    if (x >= UPBTN_X && x < UPBTN_X + UPBTN_W &&
        y >= UPBTN_Y && y < UPBTN_Y + UPBTN_H) {
        if (!recording && cloud_queue_depth > 0) {
            // Dash-initiated upload (v0.1.34+). Pop the modal locally and
            // kick the state machine, which sends Q,LIST to the Teensy and
            // drives the rest of the upload flow.
            openUploadModal("", 0);
            ufStartListing();
        }
        return;
    }

    // Start/Stop button.
    if (x >= RECBTN_X && x < RECBTN_X + RECBTN_W &&
        y >= RECBTN_Y && y < RECBTN_Y + RECBTN_H) {
        if (recording) {
            recording = false;
            Serial.printf("REC,0\n");
            return;
        }
        // START — try GPS auto-select first (only when enabled).
        if (s.auto_select_track) {
            int idx = -1;
            if (last_track_idx >= 0) {
                const float km = trackDistanceKm(g.lat_deg, g.lon_deg,
                                                 TRACKS[last_track_idx].lat,
                                                 TRACKS[last_track_idx].lon);
                if (km <= TRACKS[last_track_idx].radius_km) idx = last_track_idx;
            }
            if (idx < 0) idx = closestTrackIdx();
            if (idx >= 0) {
                if (TRACKS[idx].n_configs > 0) {
                    openConfigPicker(idx, true, true);   // from_auto, for_recording
                } else {
                    saveLastTrack(idx);
                    Serial.printf("TRACK,%s\n", active_track_name);
                    Serial.printf("REC,1\n");
                    recording = true; rec_start_ms = millis();
                }
                return;
            }
        }
        // No auto-select or no GPS match. If a track is already selected, start directly.
        if (active_track_name[0] != '\0') {
            Serial.printf("TRACK,%s\n", active_track_name);
            Serial.printf("REC,1\n");
            recording = true; rec_start_ms = millis();
            return;
        }
        // No track set at all — open picker; confirm will start recording.
        openTrackPicker(true);
    }
}

// ---------------------------------------------------------------------------
// Dash page — RPM bar, huge speed, L/R status columns, optional alert flash.
// ---------------------------------------------------------------------------
namespace {
  constexpr int RPM_BAR_X = 20;
  constexpr int RPM_BAR_Y = 10;
  constexpr int RPM_BAR_W = 760;
  constexpr int RPM_BAR_H = 80;
}

// Smooth green→yellow→red gradient between rpm_min and rpm_max.
static uint16_t rpmBarColor(uint16_t rpm) {
    const uint16_t lo = s.rpm_min, hi = s.rpm_max;
    if (hi <= lo) return TFT_GREEN;
    float ratio = (rpm <= lo) ? 0.0f
                : (rpm >= hi) ? 1.0f
                : (float)(rpm - lo) / (float)(hi - lo);
    float rf = (ratio <= 0.5f) ? (ratio * 2.0f) : 1.0f;
    float gf = (ratio <= 0.5f) ? 1.0f           : (1.0f - (ratio - 0.5f) * 2.0f);
    return tft.color565((uint8_t)(rf * 255), (uint8_t)(gf * 255), 0);
}

// Background flash color based on current RPM and alert thresholds.
// Returns the bg color the dash should paint THIS frame:
//   * TFT_BLACK if alerts disabled, RPM below alert1, or "off" half of blink.
//   * Alert1 color or alertmax color during the "on" half.
// Blink rate lerps from alert1_hz at alert1_rpm to alertmax_hz at alertmax_rpm.
static uint16_t computeBgColor() {
    if (!s.alerts_enabled) return TFT_BLACK;
    if (eng.rpm < s.alert1_rpm) return TFT_BLACK;

    uint16_t color;
    float    hz;
    if (eng.rpm >= s.alertmax_rpm) {
        color = PALETTE[s.alertmax_color_idx];
        hz    = (float)s.alertmax_hz;
    } else if (s.alertmax_rpm > s.alert1_rpm) {
        color = PALETTE[s.alert1_color_idx];
        const float frac = (float)(eng.rpm - s.alert1_rpm)
                         / (float)(s.alertmax_rpm - s.alert1_rpm);
        hz = (float)s.alert1_hz + frac * ((float)s.alertmax_hz - (float)s.alert1_hz);
    } else {
        color = PALETTE[s.alert1_color_idx];
        hz    = (float)s.alert1_hz;
    }
    if (hz < 1.0f) hz = 1.0f;
    const uint32_t halfPeriod = (uint32_t)(500.0f / hz);   // ms per half-cycle
    if (halfPeriod == 0) return color;
    const bool on = ((millis() / halfPeriod) & 1) == 0;
    return on ? color : TFT_BLACK;
}

// Cache the last-drawn value of every dynamic field. Drawing happens only
// when the new value differs from the cached one — this is what eliminates
// the per-frame flicker. Dirtied to force-redraw on bg state changes.
struct LastDrawn {
    uint16_t bg          = 0xDEAD;
    int16_t  rpm_fillW   = -1;       // last drawn bar fill width in px
    uint16_t rpm_color   = 0;        // last drawn bar fill color
    int32_t  rpm_text    = -1;       // last drawn RPM number under the bar (sentinel = redraw)
    int16_t  spd_int     = -1;       // whole-MPH integer for stable equality checks
    uint8_t  fix         = 0xFF;
    uint8_t  sats        = 0xFF;
    uint8_t  status      = 0xFF;
    int8_t   recording   = -1;       // -1=never drawn; 0=stopped; 1=recording
    uint32_t pred_lap_cs = UINT32_MAX;   // predictive lap time in centiseconds
    uint32_t last_lap_cs = UINT32_MAX;   // last completed lap time in centiseconds
    uint32_t track_tag   = UINT32_MAX;   // first 4 bytes of active_track_name; UINT32_MAX = needs redraw
    // Coolant temp / oil PSI cached state — value is x10 fixed-point (INT32_MIN
    // = redraw on next paint). The col_tag composes the current show flag,
    // the resolved colour, and the fault state into one int so any of those
    // changing forces a redraw without 3 separate fields.
    int32_t  temp_x10    = INT32_MIN;
    uint32_t temp_col_tag = UINT32_MAX;
    int32_t  psi_x10     = INT32_MIN;
    uint32_t psi_col_tag  = UINT32_MAX;
    int32_t  afr_x10     = INT32_MIN;
    uint32_t afr_col_tag  = UINT32_MAX;
    // REC badge state: composite tag of (dash recording bit, teensy ack bit,
    // mismatch-warning bit), plus the last-drawn sample count and queue depth.
    uint8_t  rec_badge_tag = 0xFF;
    uint32_t rec_samples  = UINT32_MAX;
    uint32_t cld_queue    = UINT32_MAX;
    // Composite tag for the manual UPLOAD button: low bit = visible, upper
    // bits = queue count. Sentinel UINT32_MAX = needs redraw.
    uint32_t upbtn_tag    = UINT32_MAX;
};
static LastDrawn ld;
static void invalidateAll() {
    ld.rpm_fillW = -1; ld.rpm_text = -1; ld.spd_int = -1;
    ld.fix = 0xFF; ld.sats = 0xFF; ld.status = 0xFF;
    ld.recording = -1;
    ld.rec_badge_tag = 0xFF; ld.rec_samples = UINT32_MAX; ld.cld_queue = UINT32_MAX;
    ld.upbtn_tag = UINT32_MAX;
    ld.pred_lap_cs = UINT32_MAX; ld.last_lap_cs = UINT32_MAX;
    ld.track_tag   = UINT32_MAX;
    ld.temp_x10 = INT32_MIN; ld.temp_col_tag = UINT32_MAX;
    ld.psi_x10  = INT32_MIN; ld.psi_col_tag  = UINT32_MAX;
    ld.afr_x10  = INT32_MIN; ld.afr_col_tag  = UINT32_MAX;
}

static void drawRecordButton() {
    const uint16_t fill   = recording ? TFT_RED   : TFT_GREEN;
    const uint16_t border = TFT_WHITE;
    const char*    label  = recording ? "STOP"    : "START";

    if (dash_sprites_ready) {
        spr_recbtn.fillSprite(fill);
        spr_recbtn.drawRect(0, 0, RECBTN_W,     RECBTN_H,     border);
        spr_recbtn.drawRect(1, 1, RECBTN_W - 2, RECBTN_H - 2, border);
        spr_recbtn.drawRect(2, 2, RECBTN_W - 4, RECBTN_H - 4, border);
        spr_recbtn.setFont(&fonts::Font4);
        spr_recbtn.setTextSize(1);
        spr_recbtn.setTextDatum(textdatum_t::middle_center);
        spr_recbtn.setTextColor(TFT_WHITE);
        spr_recbtn.drawString(label, RECBTN_W / 2, RECBTN_H / 2);
        spr_recbtn.pushSprite(RECBTN_X, RECBTN_Y);
    } else {
        tft.fillRect(RECBTN_X, RECBTN_Y, RECBTN_W, RECBTN_H, fill);
        tft.drawRect(RECBTN_X,     RECBTN_Y,     RECBTN_W,     RECBTN_H,     border);
        tft.drawRect(RECBTN_X + 1, RECBTN_Y + 1, RECBTN_W - 2, RECBTN_H - 2, border);
        tft.drawRect(RECBTN_X + 2, RECBTN_Y + 2, RECBTN_W - 4, RECBTN_H - 4, border);
        tft.setFont(&fonts::Font4);
        tft.setTextSize(1);
        tft.setTextDatum(textdatum_t::middle_center);
        tft.setTextColor(TFT_WHITE, fill);
        tft.drawString(label, RECBTN_X + RECBTN_W / 2, RECBTN_Y + RECBTN_H / 2);
    }
}
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
